sampidevkit/PIC16FDevKit/TUT/B02_Config_GPIO/Cfg_GPIO_XC8.pdf

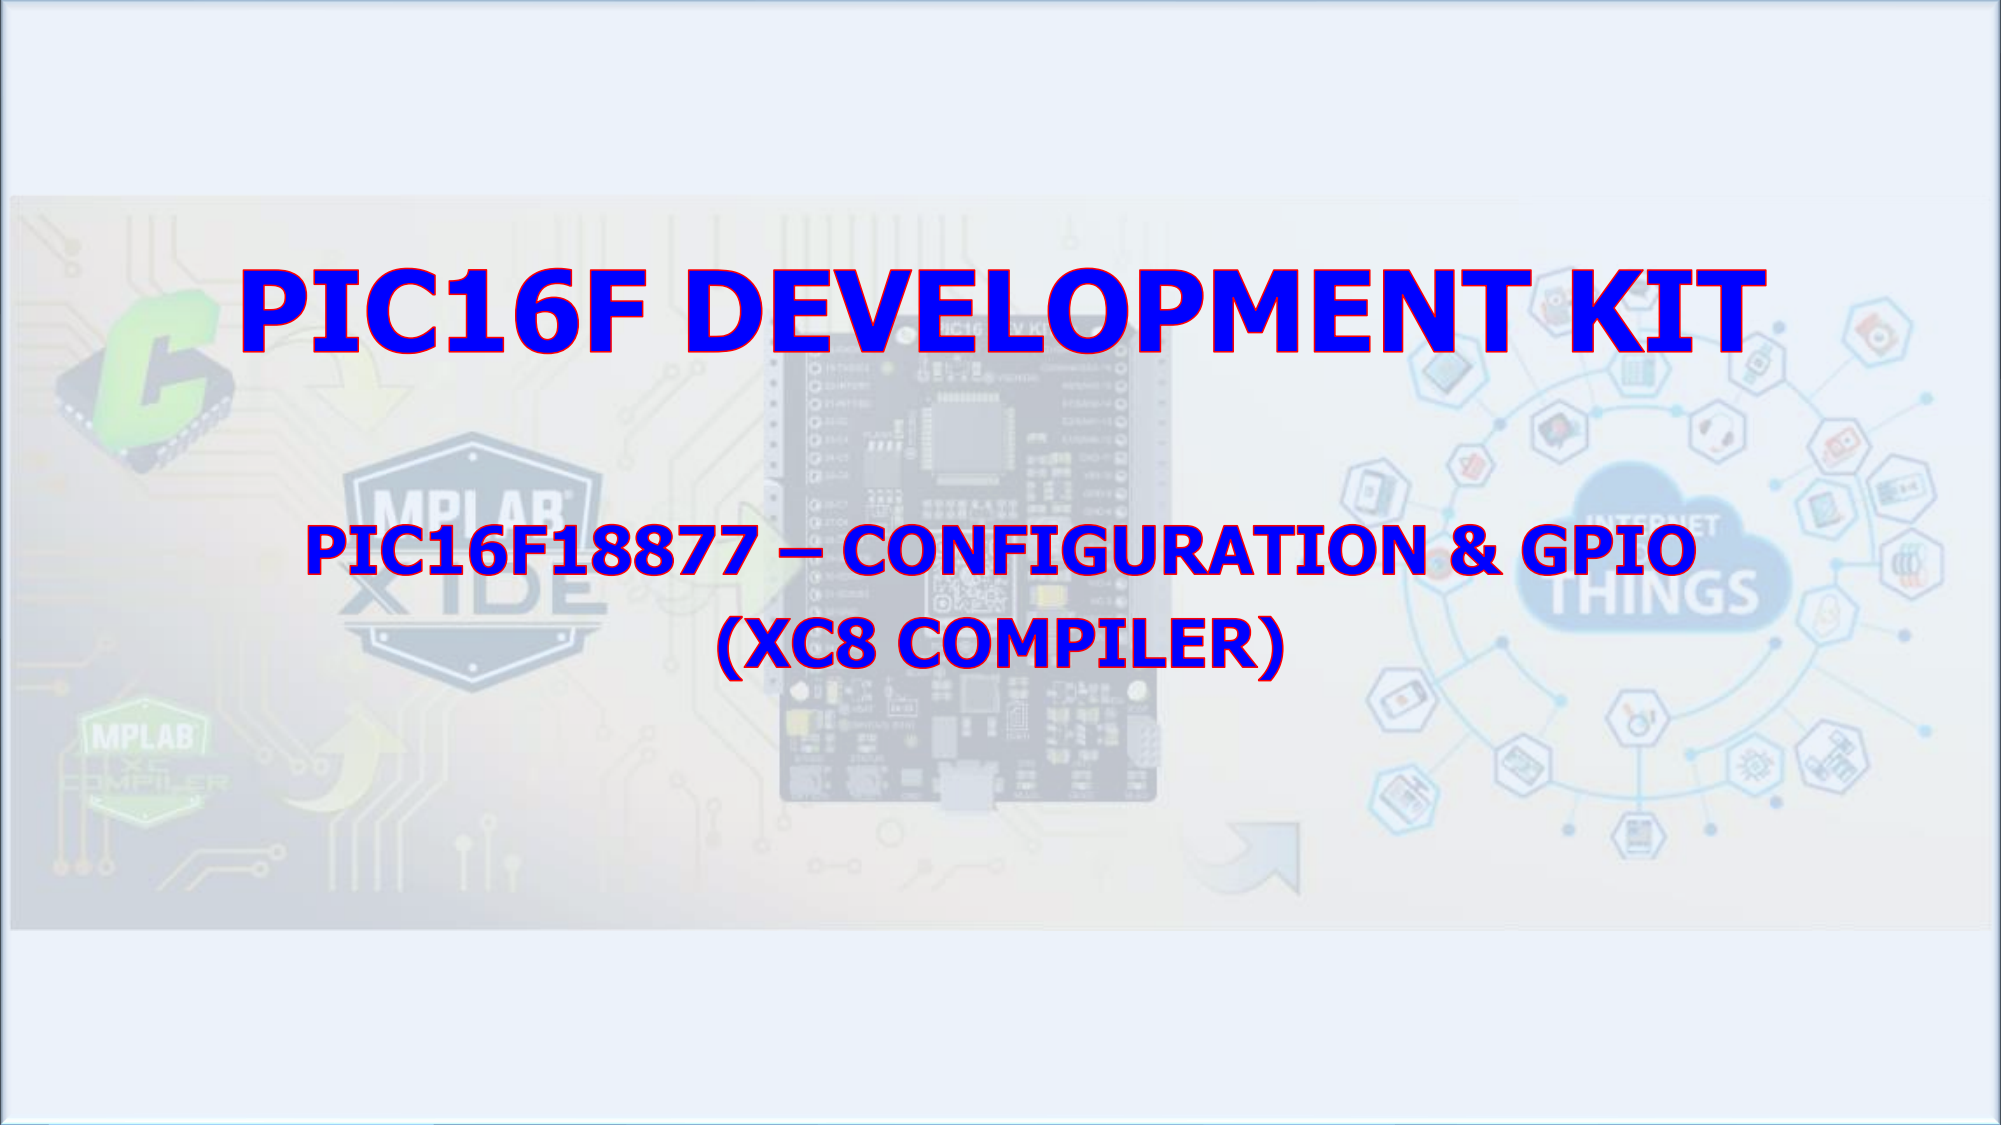
[picture p91: page 1]

# NỘI DUNG

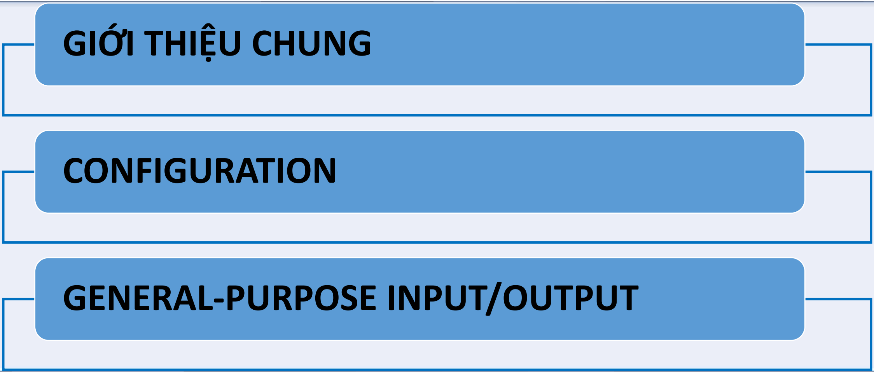
[picture p92: figure]
GIỚI THIỆU CHUNG; CONFIGURATION; GENERAL-PURPOSE INPUT/OUTPUT

# GIỚI THIỆU CHUNG

# 1. HỆ THỐNG VI ĐIỀU KHIỂN

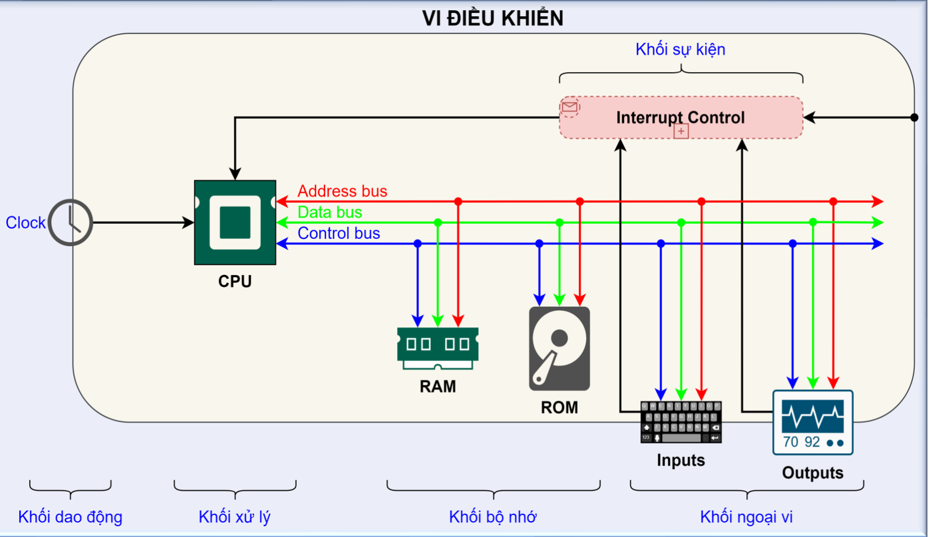
[picture p93: figure]

# 1. Khối dao động 2. Khối xử lý 3. Khối bộ nhớ 4. Khối ngoại vi 5. Khối sự kiện 6. Các khối khác:

Quản lý nguồn,

# Gỡ lỗi, …

GIỚI THIỆU CHUNG

CONFIGURATION

GENERAL-PURPOSE INPUT/OUTPUT

# GIỚI THIỆU CHUNG

# 2. CÔNG CỤ PHÁT TRIỂN

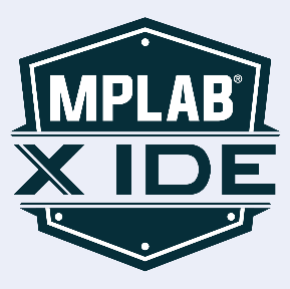
[picture p94: figure]

# 1. MPLAB X IDE/ PIC C IDE Môi trường soạn thảo, định dạng, gỡ lỗi, …

# 2. MPLAB XC8/ CCS C

Chuyển đổi ngôn ngữ C/Asm sang mã thực thi.

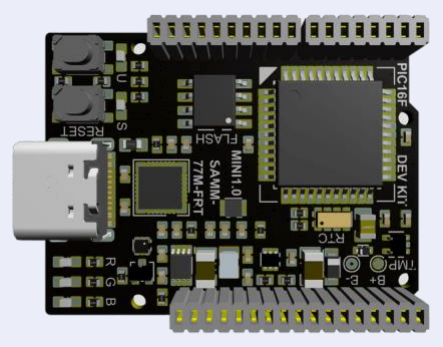
[picture p95: figure]

# 3. Evaluation Kit

GIỚI THIỆU CHUNG

CONFIGURATION

GENERAL-PURPOSE INPUT/OUTPUT

# GIỚI THIỆU CHUNG

# 3. TÀI LIỆU KỸ THUẬT

1. Datasheet: DS40001825F (https://ww1.microchip.com/downloads/en/DeviceDoc/PIC16LF1885777_Data_Sheet_40001825F.pdf)
2. Programming Specifications: DS40001753B (https://ww1.microchip.com/downloads/en/DeviceDoc/40001753B.pdf)

# 3. Application Notes:

# https://www.microchip.com/en-us/application-notes

# 4. Code Examples:

# https://www.microchip.com/doclisting/CodeExamplesByFunc.aspx

GIỚI THIỆU CHUNG

CONFIGURATION

GENERAL-PURPOSE INPUT/OUTPUT

# CONFIGURATION

# 1. CẤU TRÚC BỘ NHỚ

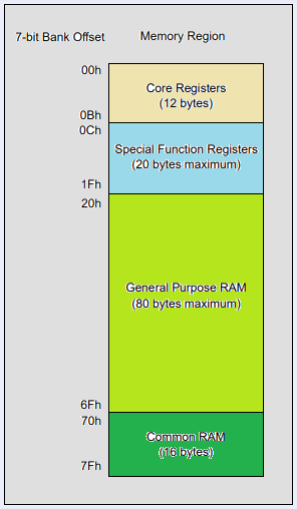
[picture p96: figure]

# Để làm việc với vi điều khiển cần:

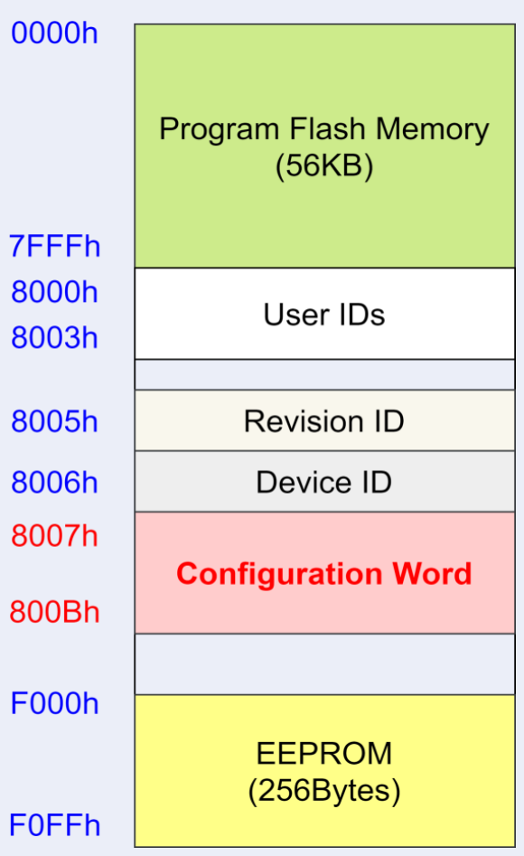
[picture p97: figure]

❑ Cấu hình được chip.
❑ Quản lý được bộ nhớ.
❑ Quản lý được ngoại vi.

# Xem thêm:

→DS40001753B (https://ww1.microchip.com/downloads/en/DeviceDoc/40001753B.pdf) – trang 3.
→DS40001825F (https://ww1.microchip.com/downloads/en/DeviceDoc/PIC16LF1885777_Data_Sheet_40001825F.pdf) – trang 39.

GIỚI THIỆU CHUNG

CONFIGURATION

GENERAL-PURPOSE INPUT/OUTPUT

# CONFIGURATION

# 2. CẤU HÌNH CHIP

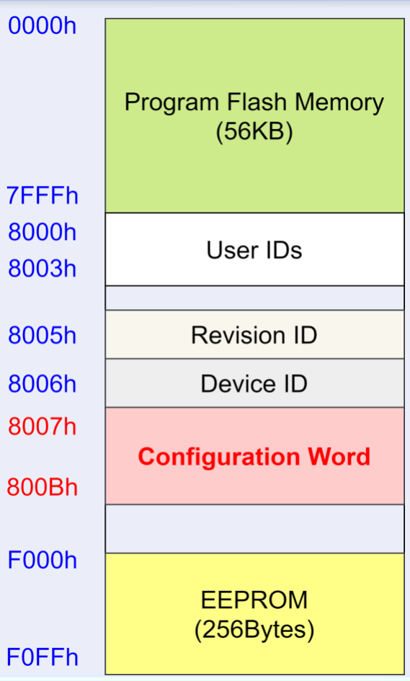
[picture p98: figure]

# ❑ Quy định các tính năng cụ thể của chip, bao gồm: dao động, quản lý lỗi, quản lý nguồn, tính năng bảo mật, …

# ❑ Các bit cấu hình là cố định, không thay đổi trong quá

trình hoạt động.

# ❑ Vùng nhớ cấu hình chip có độ dài 5 word (5x2byte):

## Word 1: Oscillator Word 2: Supervisors Word 3: Watchdog Word 4: Memory Word 5: Code protection

GIỚI THIỆU CHUNG

CONFIGURATION

GENERAL-PURPOSE INPUT/OUTPUT

# CONFIGURATION

# 2. CẤU HÌNH CHIP

GIỚI THIỆU CHUNG

CONFIGURATION

GENERAL-PURPOSE INPUT/OUTPUT

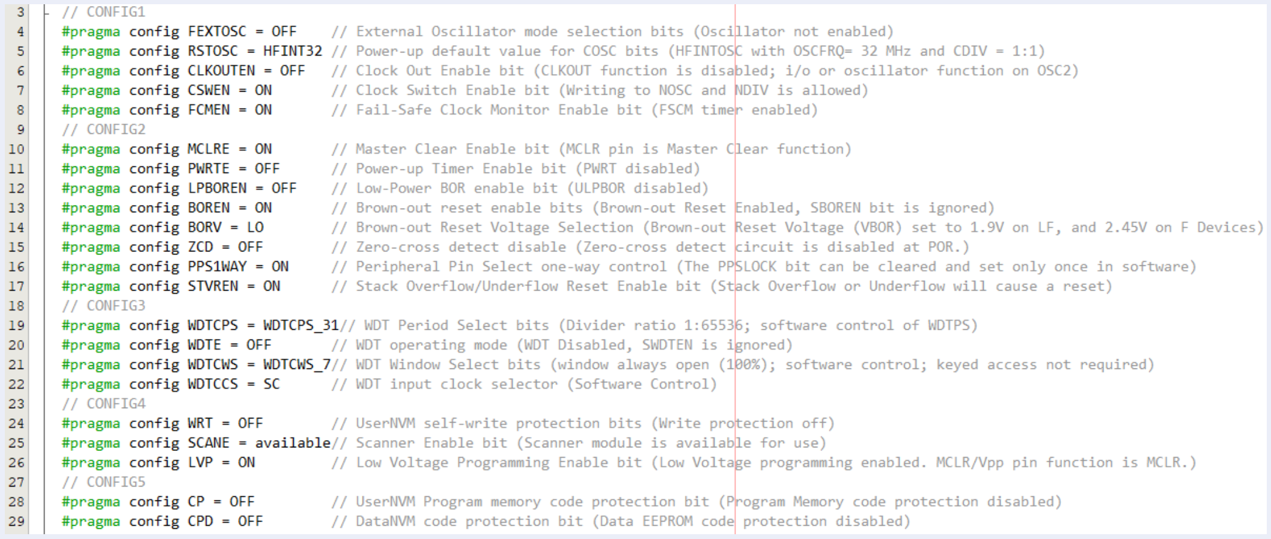
[picture p99: figure]

# CONFIGURATION

# 3. CẤU DAO ĐỘNG

# ❑ PIC16F18877 có 2 nhóm dao động:

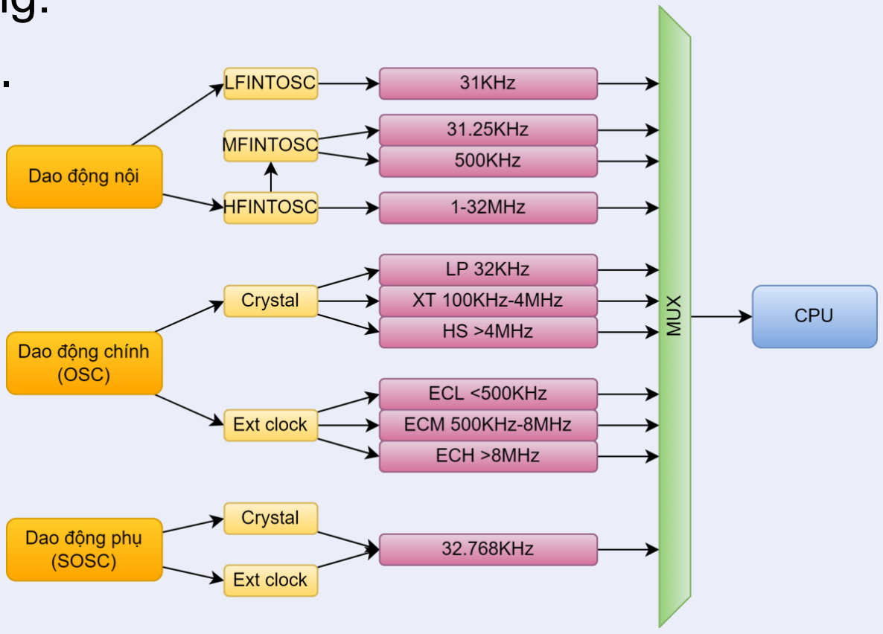
[picture p100: figure]

- Dao động nội: 31KHz đến 32MHz.

# - Dao động ngoài:

- Clock chính OSC: lên đến 32MHz.
- Clock phụ SOSC: 32768Hz.
❑ Tốc độ xử lý: FCPU=FOSC/4.

GIỚI THIỆU CHUNG

CONFIGURATION

GENERAL-PURPOSE INPUT/OUTPUT

# CONFIGURATION

# 3. CẤU DAO ĐỘNG

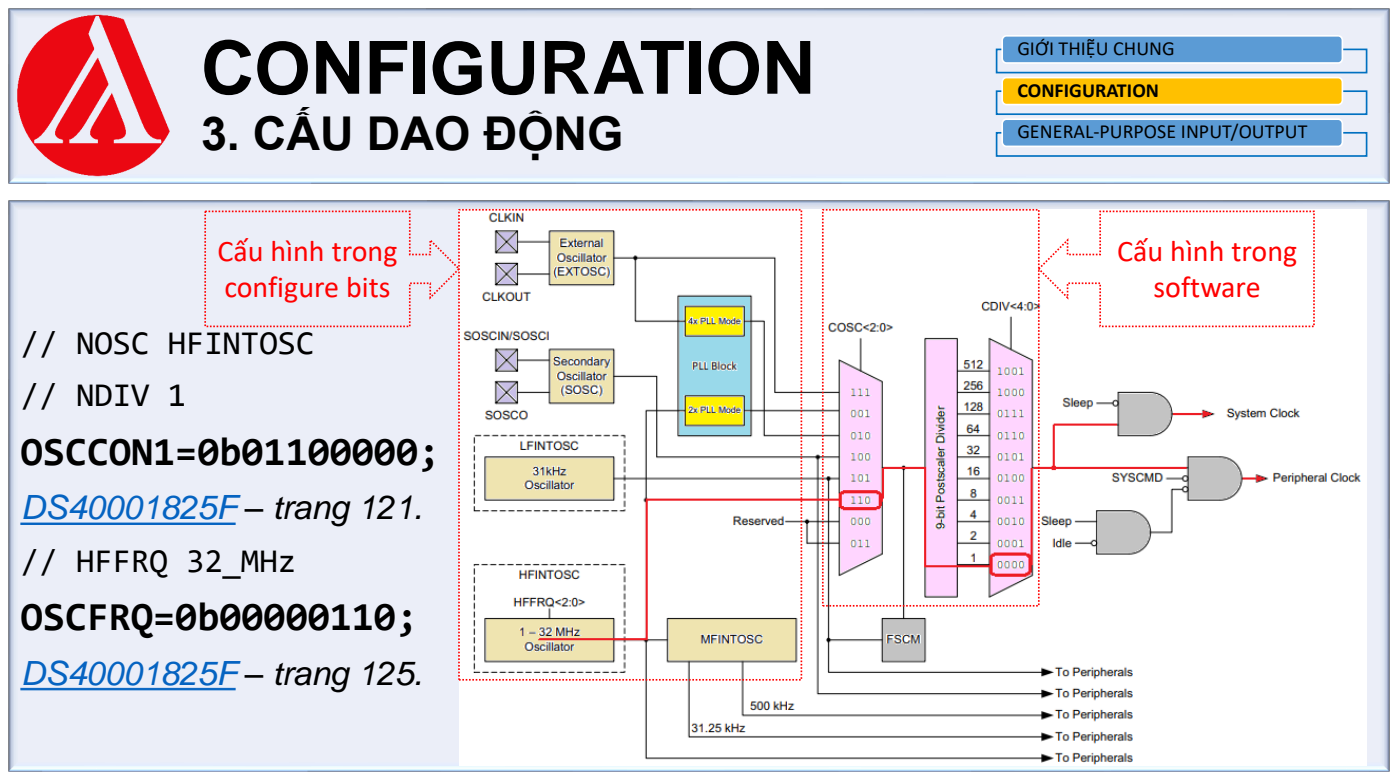
[picture p101: page 10]

## // NOSC HFINTOSC // NDIV 1

OSCCON1=0b01100000;

DS40001825F (https://ww1.microchip.com/downloads/en/DeviceDoc/PIC16LF1885777_Data_Sheet_40001825F.pdf) – trang 121.

## // HFFRQ 32_MHz

OSCFRQ=0b00000110;

DS40001825F (https://ww1.microchip.com/downloads/en/DeviceDoc/PIC16LF1885777_Data_Sheet_40001825F.pdf) – trang 125.

GIỚI THIỆU CHUNG

CONFIGURATION

GENERAL-PURPOSE INPUT/OUTPUT

## Cấu hình trong software

## Cấu hình trong configure bits

# GPIO

# 1. I/O PORTS

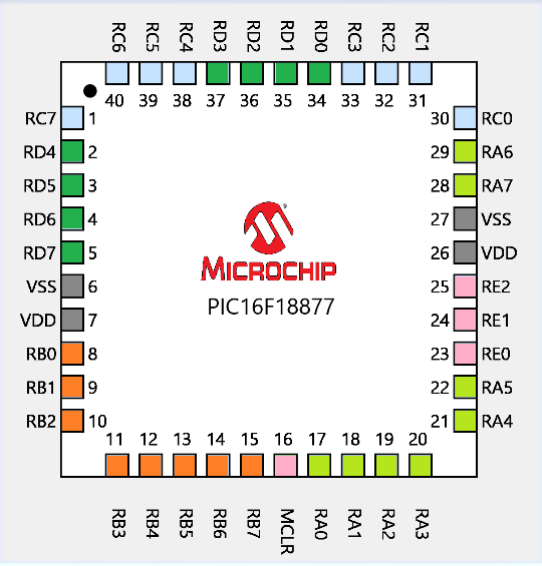
[picture p102: figure]

# ❑ PIC16F18877 có 5 port:

Port A, B, C, D: 8 I/O.

# Port E: 4 I/O. Có 1 I/O được mặc định

chức năng MCLR.

GIỚI THIỆU CHUNG

CONFIGURATION

GENERAL-PURPOSE INPUT/OUTPUT

# GPIO

# 1. I/O PORTS

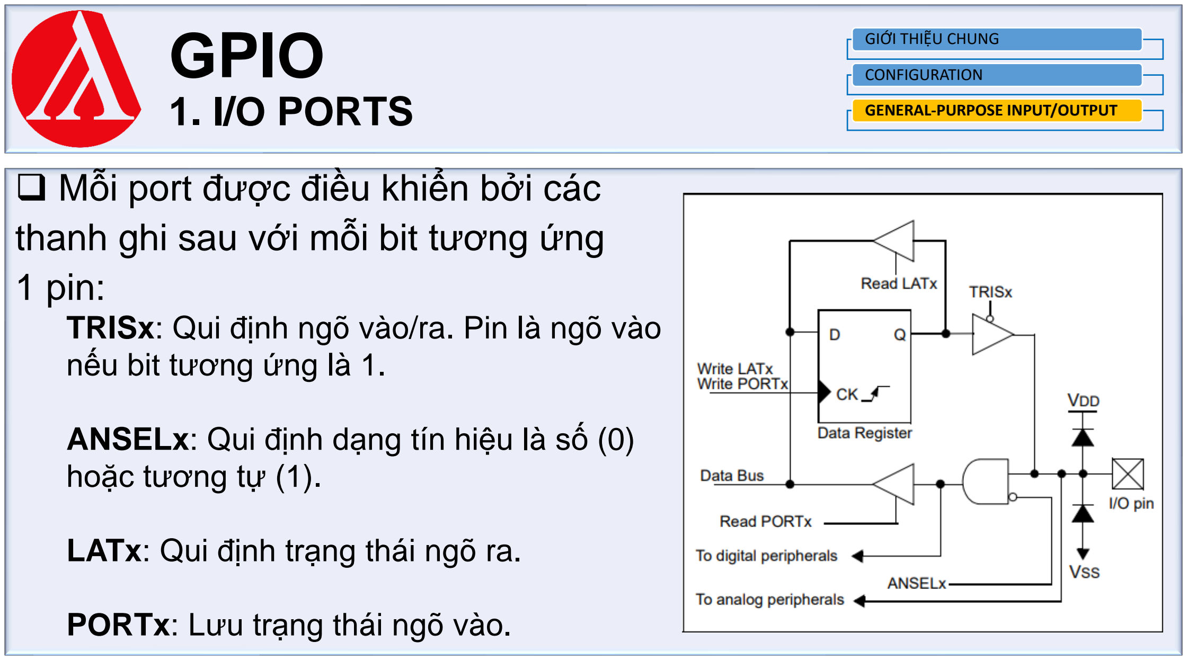
[picture p103: page 12]

# ❑ Mỗi port được điều khiển bởi các thanh ghi sau với mỗi bit tương ứng 1 pin:

# TRISx: Qui định ngõ vào/ra. Pin là ngõ vào

nếu bit tương ứng là 1.

# ANSELx: Qui định dạng tín hiệu là số (0)

hoặc tương tự (1).

LATx: Qui định trạng thái ngõ ra.

PORTx: Lưu trạng thái ngõ vào.

GIỚI THIỆU CHUNG

CONFIGURATION

GENERAL-PURPOSE INPUT/OUTPUT

# GPIO

# 1. I/O PORTS

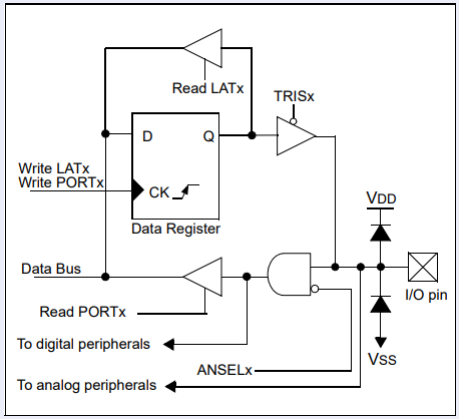
[picture p104: figure]

WPUx: Cấu hình điện trở kéo lên.

# INLVLx: Qui định chuẩn logic TTL hoặc CMOS. (Mặc định)

# SLRCONx: Qui định tốc độ thay đổi trạng thái. (Mặc định)

# ODCONx: Cấu hình ngõ ra cực

nguồn hở.

GIỚI THIỆU CHUNG

CONFIGURATION

GENERAL-PURPOSE INPUT/OUTPUT

# GPIO

# 2. DIGITAL OUTPUTS

# Qui trình cấu hình:

✓ Cấu hình tín hiệu số: ANSELxbits.ANSxy=0;
✓ Cấu hình ngõ ra: TRISxbits.TRISxy=0;

# ✓ Cấu hình cực nguồn: ODCONxbits.ODCxy=0; // Push-Pull

| ODCONxbits.ODCxy=1; // Open-drain
✓ Đặt trạng thái: | LATxbits.LATxy=0; // Set low
| LATxbits.LATxy=1; // Set high

GIỚI THIỆU CHUNG

CONFIGURATION

GENERAL-PURPOSE INPUT/OUTPUT

# GPIO

# 2. DIGITAL OUTPUTS

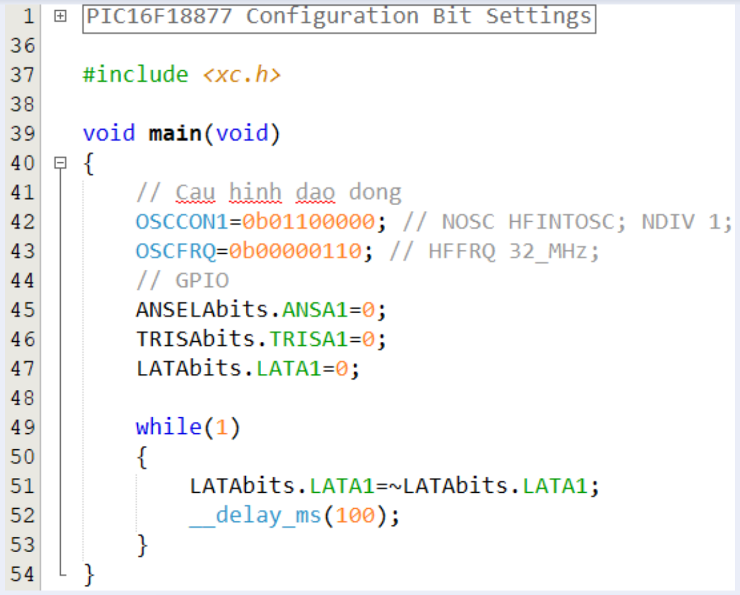
[picture p105: figure]

# Ví dụ:

GIỚI THIỆU CHUNG

CONFIGURATION

GENERAL-PURPOSE INPUT/OUTPUT

# GPIO

# 3. DIGITAL INPUTS

# Qui trình cấu hình:

✓ Cấu hình tín hiệu số: ANSELxbits.ANSxy=0;
✓ Cấu hình ngõ vào: TRISxbits.TRISxy=1;

# ✓ Cấu hình điện trở kéo: WPUAbits.WPUxy=0; // No pull-up

| WPUAbits.WPUxy=1; // Pull-up
✓ Đọc trạng thái: | bool x=PORTxbits.Rxy;

GIỚI THIỆU CHUNG

CONFIGURATION

GENERAL-PURPOSE INPUT/OUTPUT

# GPIO

# 3. DIGITAL INPUTS

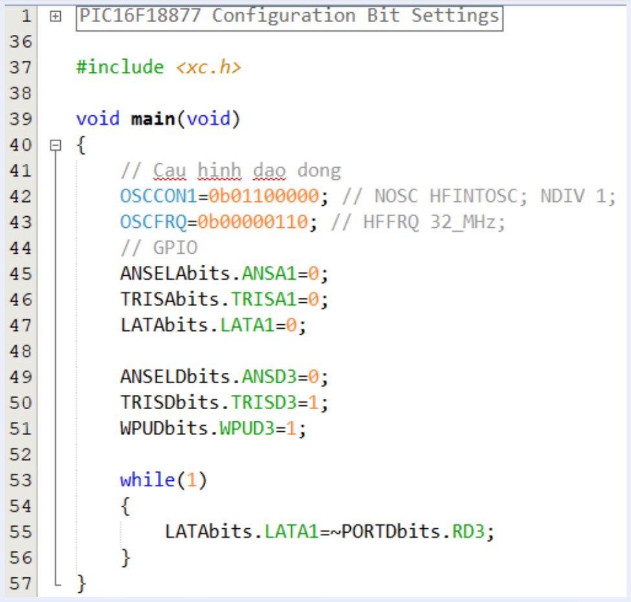
[picture p106: figure]

# Ví dụ

:

GIỚI THIỆU CHUNG

CONFIGURATION

GENERAL

-PURPOSE INPUT/OUTPUT

# GPIO

# 3. DIGITAL INPUTS

# Simple button:

GIỚI THIỆU CHUNG

CONFIGURATION

GENERAL-PURPOSE INPUT/OUTPUT

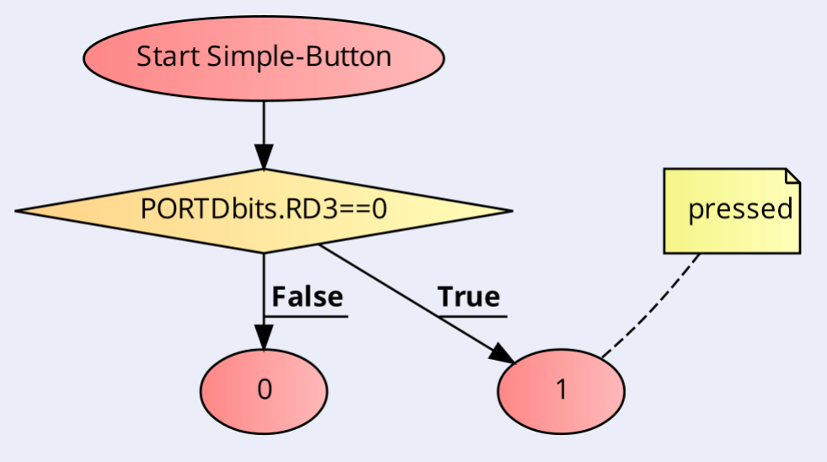
[picture p107: figure]

# GPIO

# 3. DIGITAL INPUTS

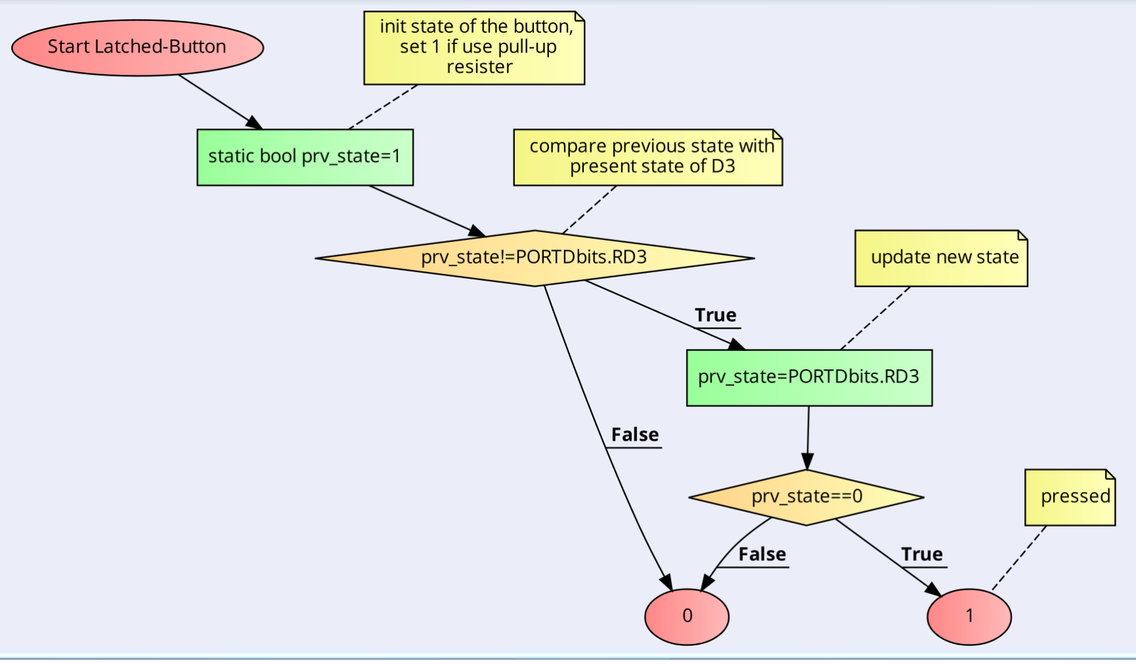
[picture p108: figure]

# Latched button:

GIỚI THIỆU CHUNG

CONFIGURATION

GENERAL-PURPOSE INPUT/OUTPUT

# GPIO

# 3. DIGITAL INPUTS

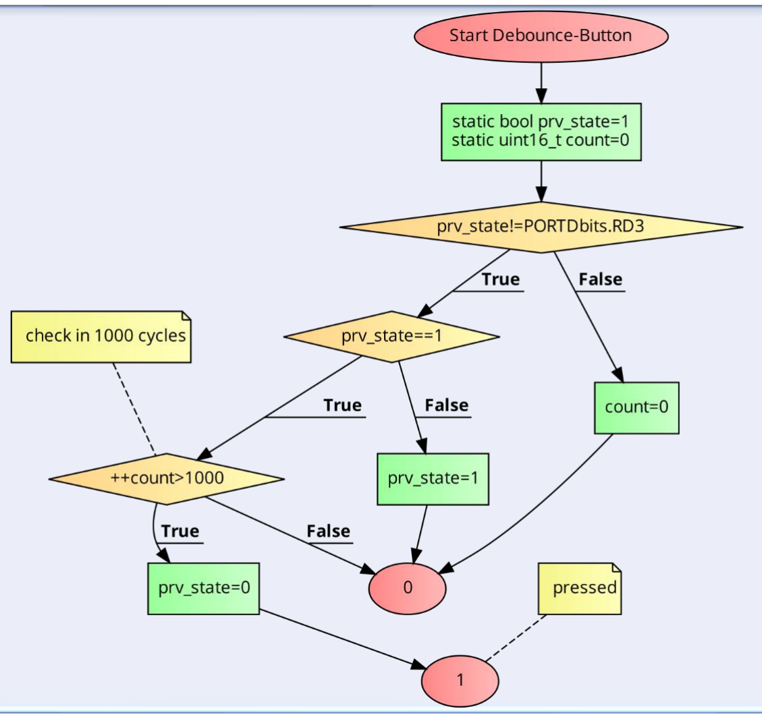
[picture p109: figure]

# Debounce button:

GIỚI THIỆU CHUNG

CONFIGURATION

GENERAL-PURPOSE INPUT/OUTPUT
