sampidevkit/PIC16FDevKit/Docs/Ports.png

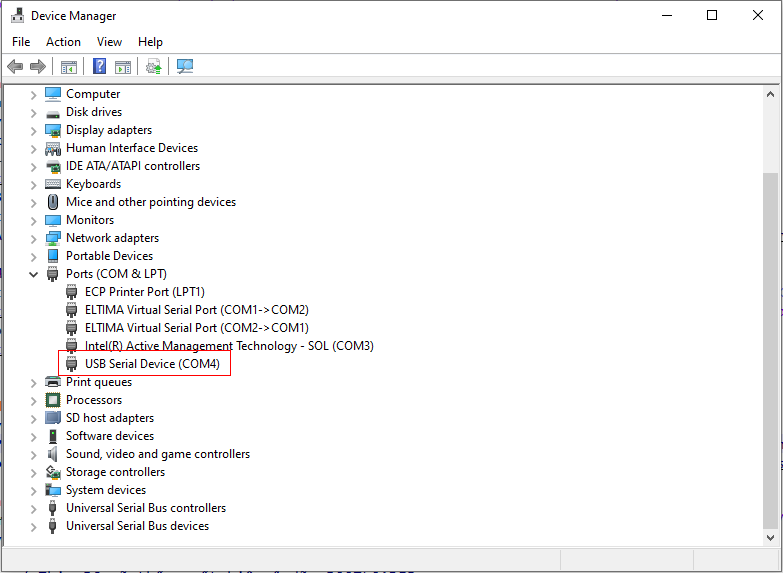
Docs/Ports.png
