sampidevkit/PIC16FDevKit/Docs/Qwiic.bmp

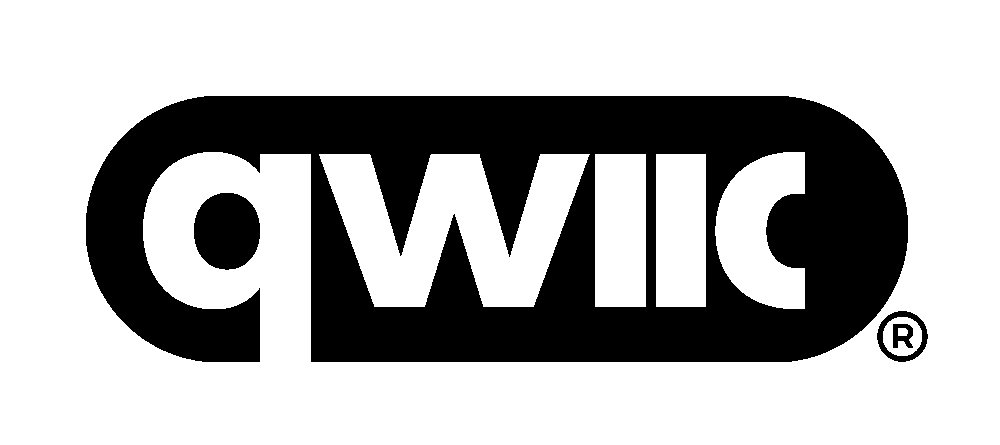
Docs/Qwiic.bmp
