sampidevkit/PIC16FDevKit/Docs/TerminalCfg.png

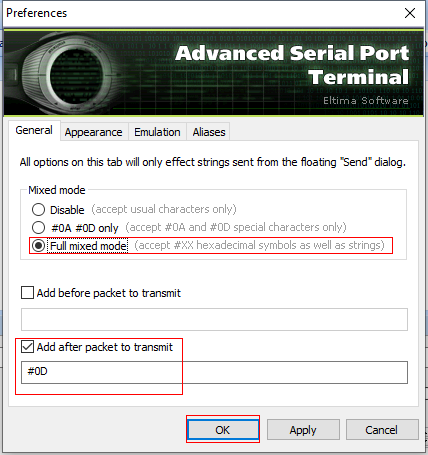
Docs/TerminalCfg.png
