sampidevkit/PIC16FDevKit/Docs/TerminalOpen.png

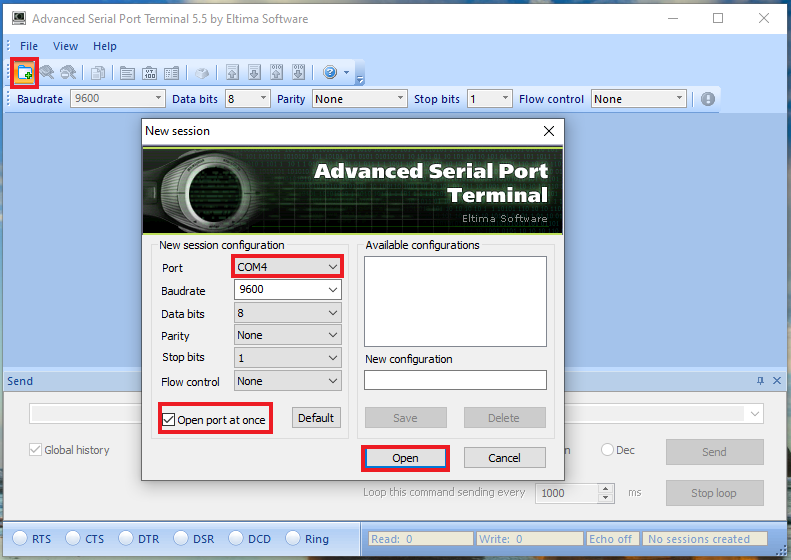
Docs/TerminalOpen.png
