sampidevkit/PIC16FDevKit/Docs/TrainingProgram.drawio.png

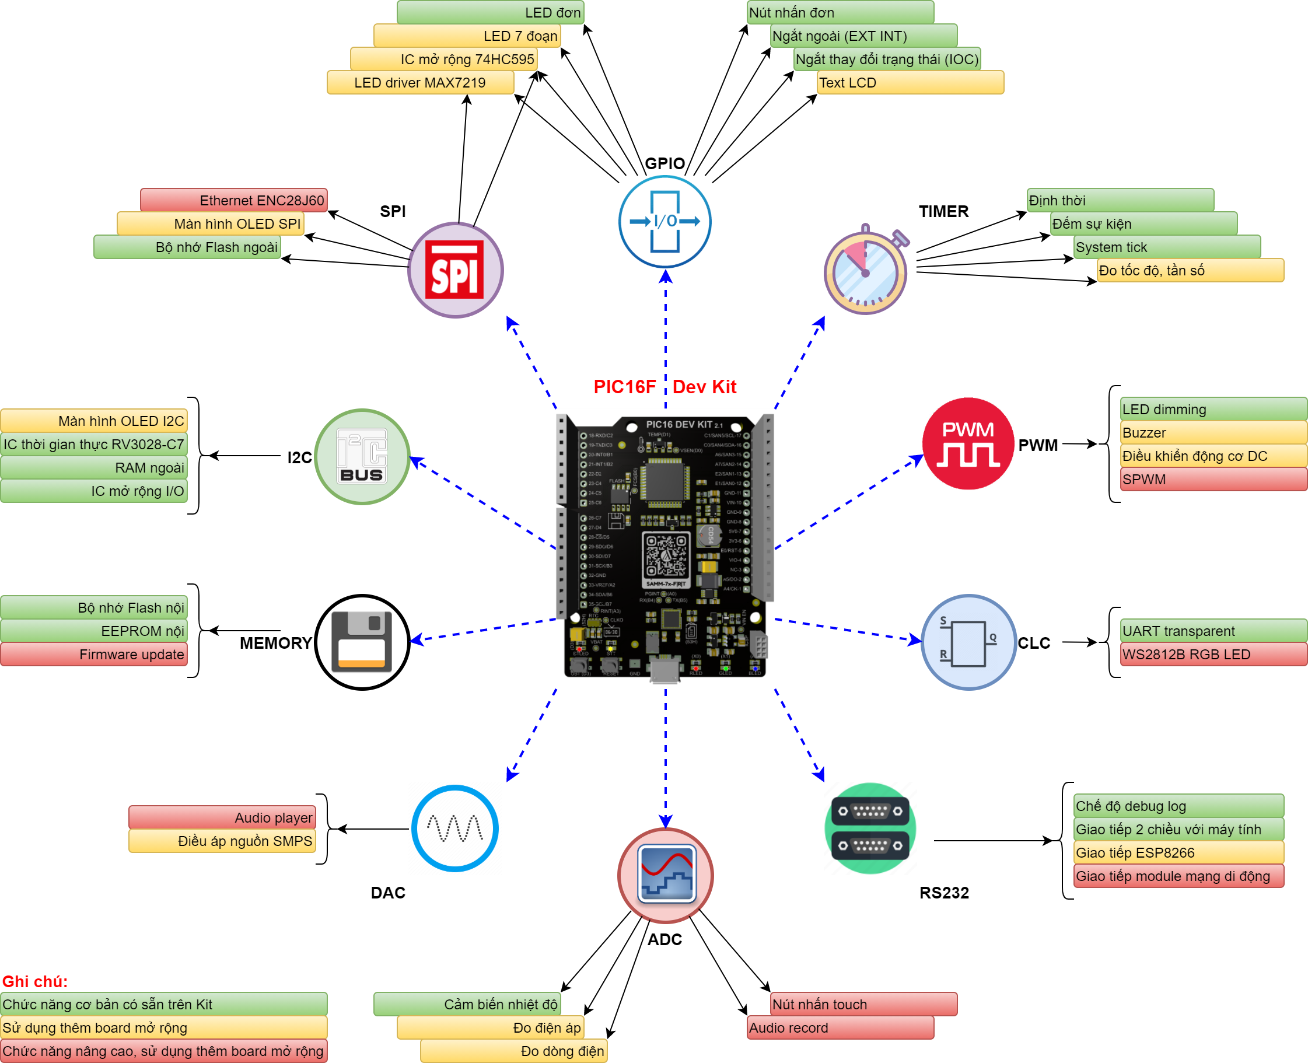
Docs/TrainingProgram.drawio.png
