sampidevkit/PIC16FDevKit/FW/PG_v2.X/App Project Tree.png

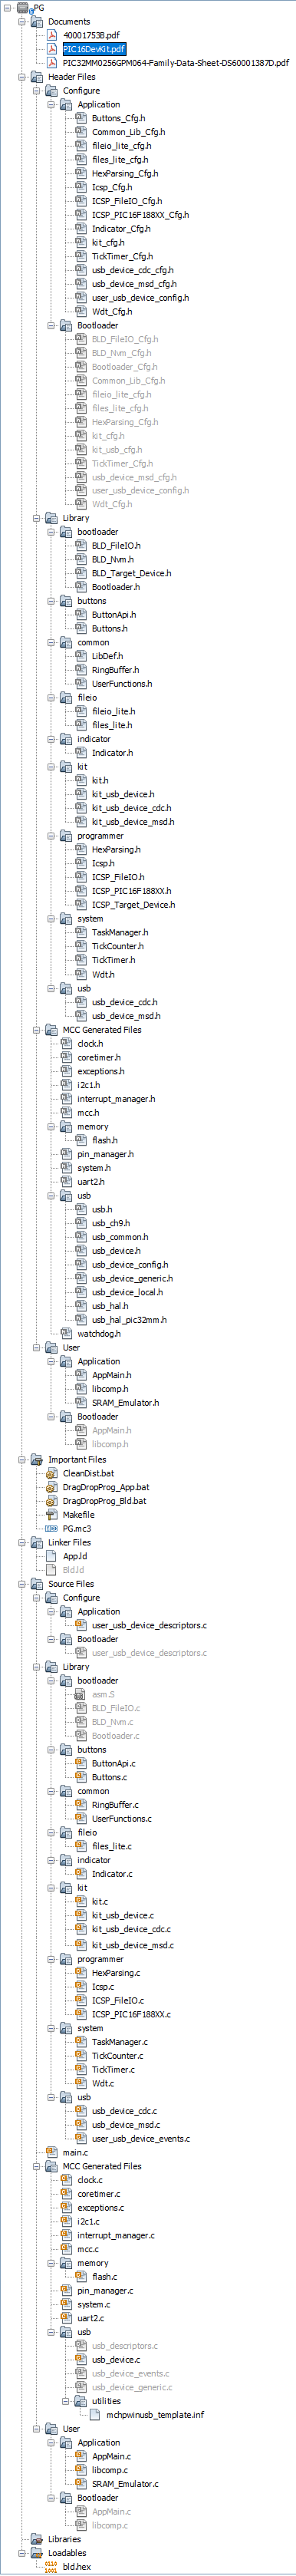
FW/PG_v2.X/App Project Tree.png
