sampidevkit/PIC16FDevKit/FW/PG_v2.X/BLD Project Tree.png

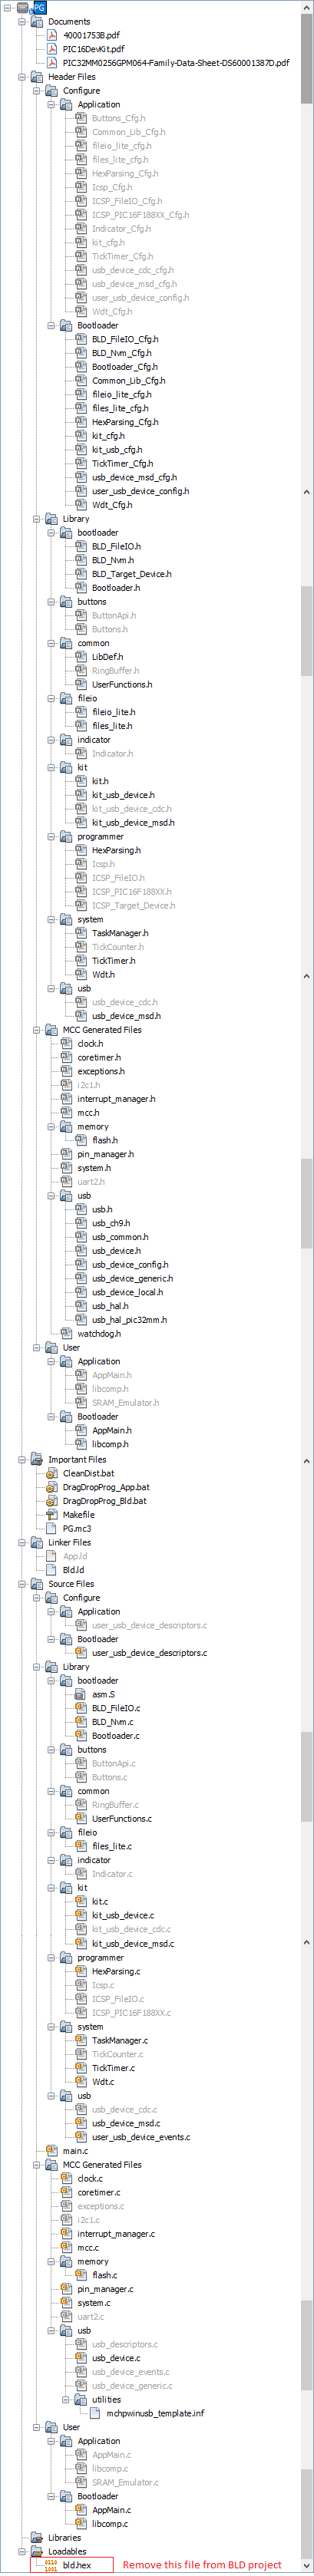
FW/PG_v2.X/BLD Project Tree.png
