sampidevkit/PIC16FDevKit/FW/TG_v2.X/ScreenShot_20220130204213.png

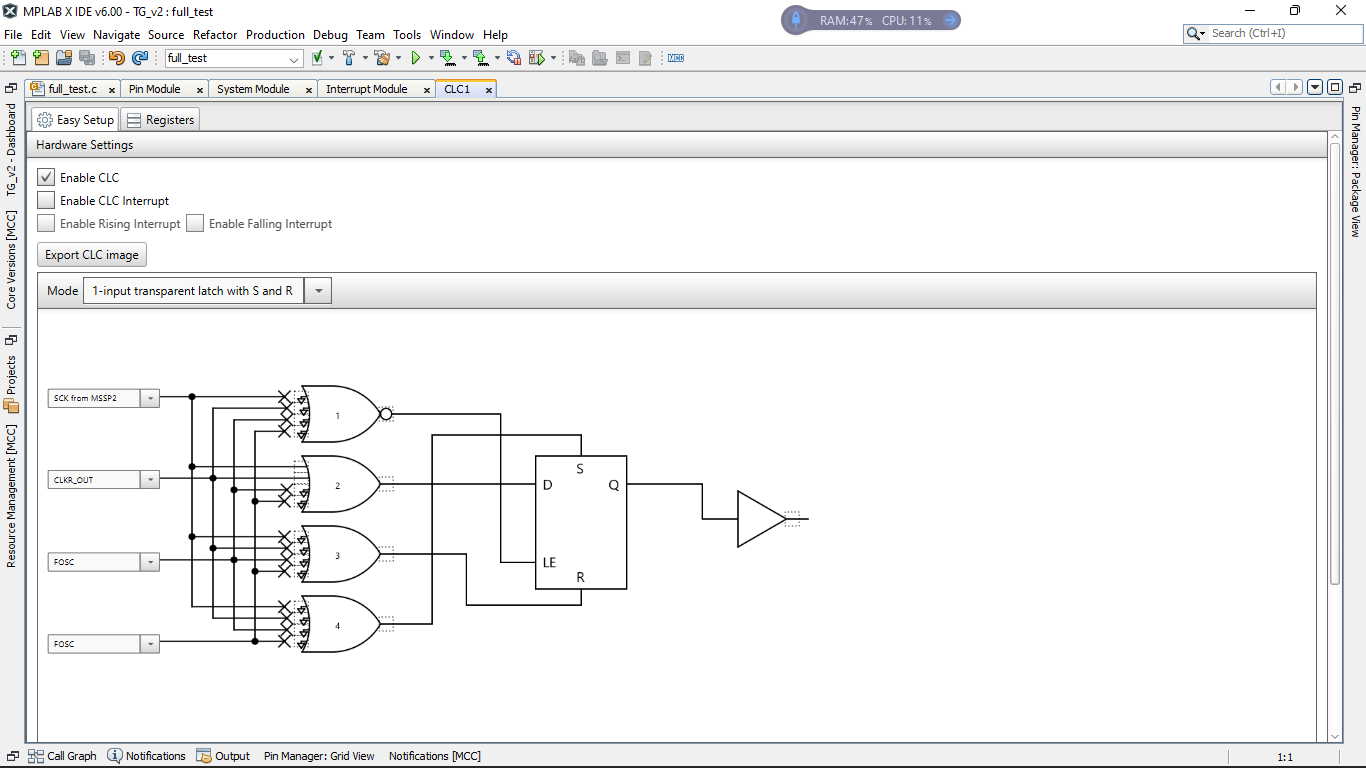
FW/TG_v2.X/ScreenShot_20220130204213.png
