sampidevkit/PIC16FDevKit/HW/Product/Mini/Picture/ScreenShot_20220119223752.png

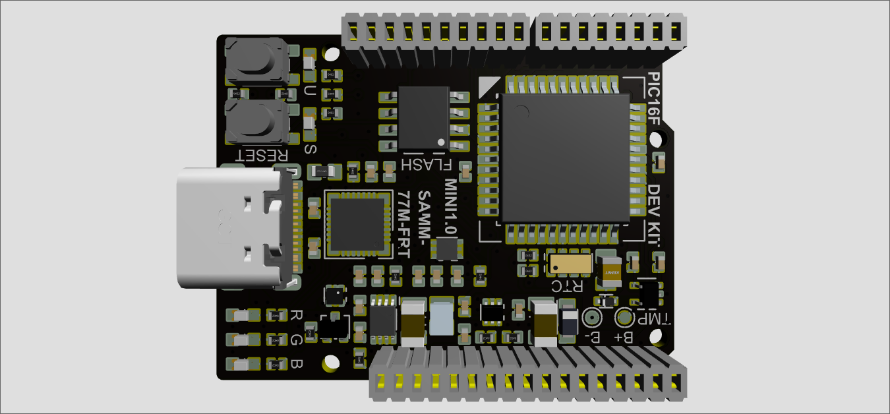
HW/Product/Mini/Picture/ScreenShot_20220119223752.png
