sampidevkit/PIC16FDevKit/HW/Product/Mini/Picture/ScreenShot_20220119223829.png

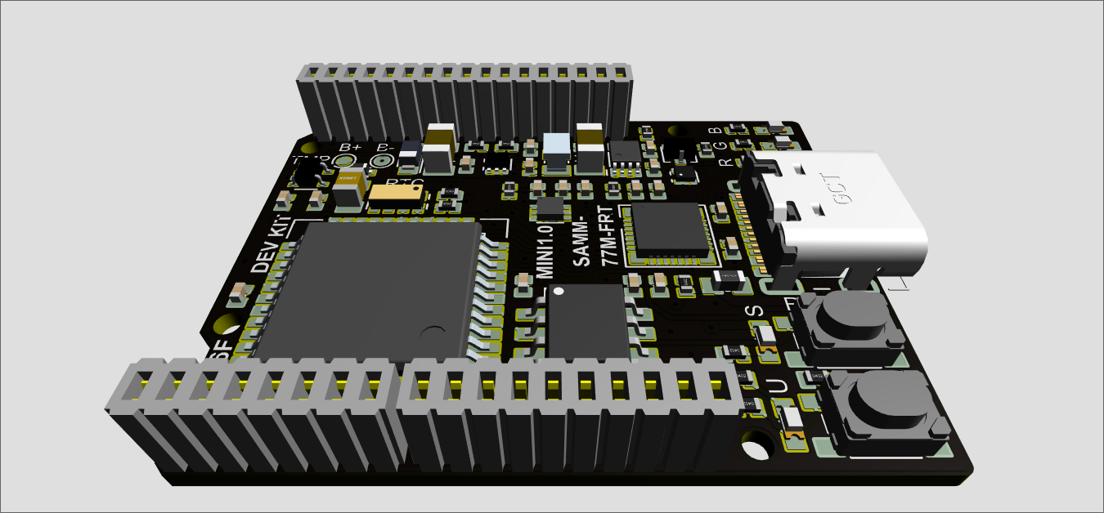
HW/Product/Mini/Picture/ScreenShot_20220119223829.png
