sampidevkit/PIC16FDevKit/HW/Product/Standard/Picture/PIC16DevKit Asm.png

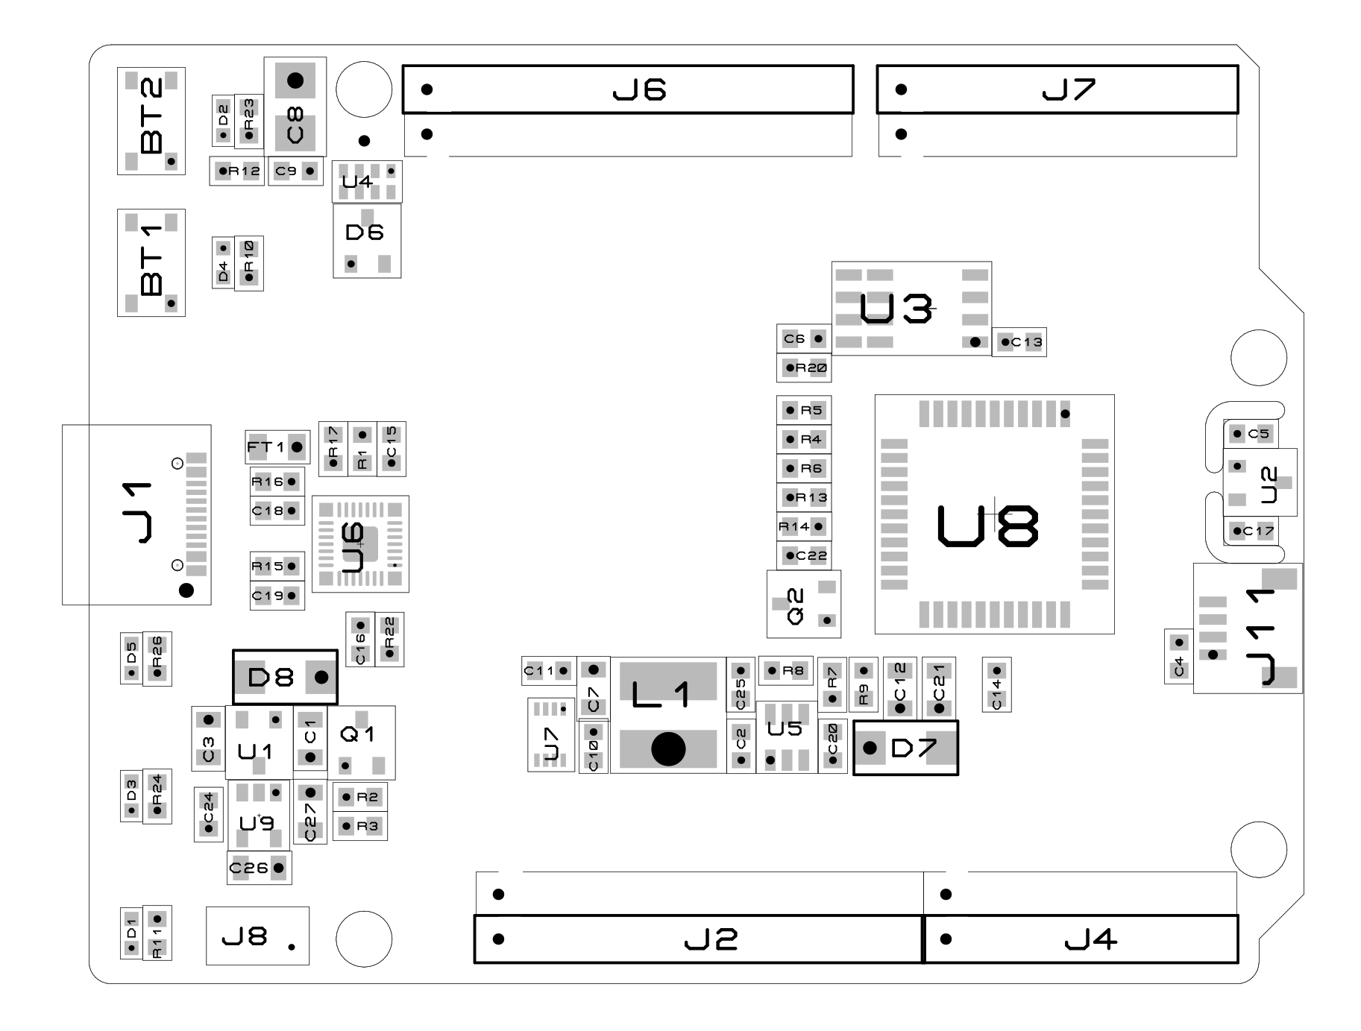
HW/Product/Standard/Picture/PIC16DevKit Asm.png
