sampidevkit/PIC16FDevKit/HW/Product/Standard/Picture/PIC16DevKit Top.png

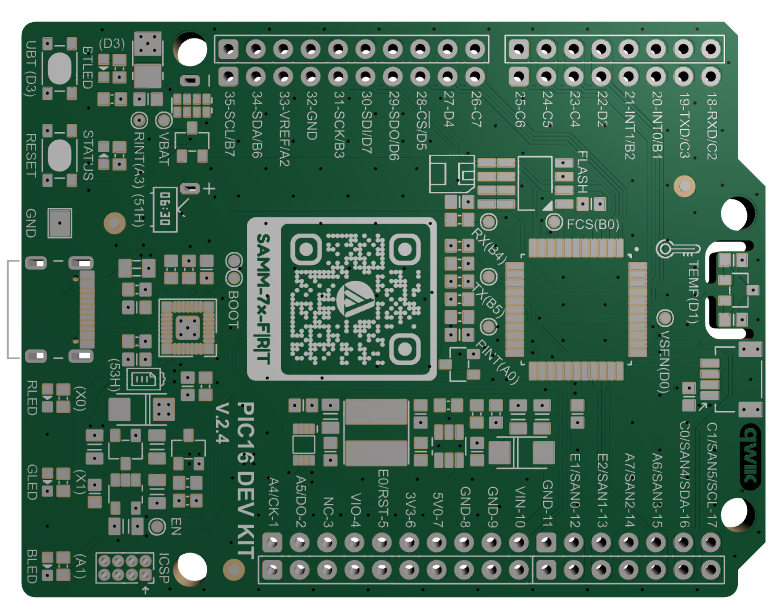
HW/Product/Standard/Picture/PIC16DevKit Top.png
