sampidevkit/PIC16FDevKit/HW/Product/Standard/Picture/PIC16DevKit.png

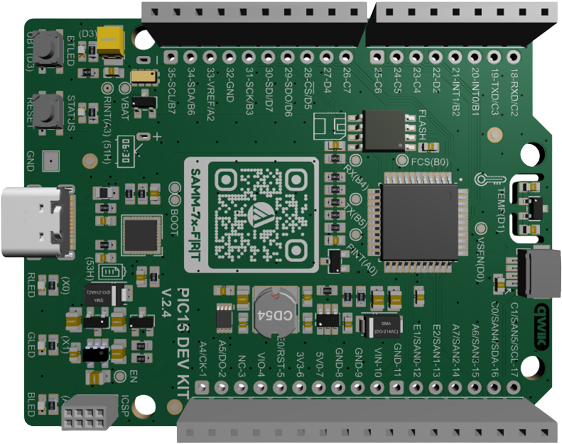
HW/Product/Standard/Picture/PIC16DevKit.png
