sampidevkit/PIC16FDevKit/TUT/B02_Config_GPIO/B02_1_XC8.X/B02_1 (10).png

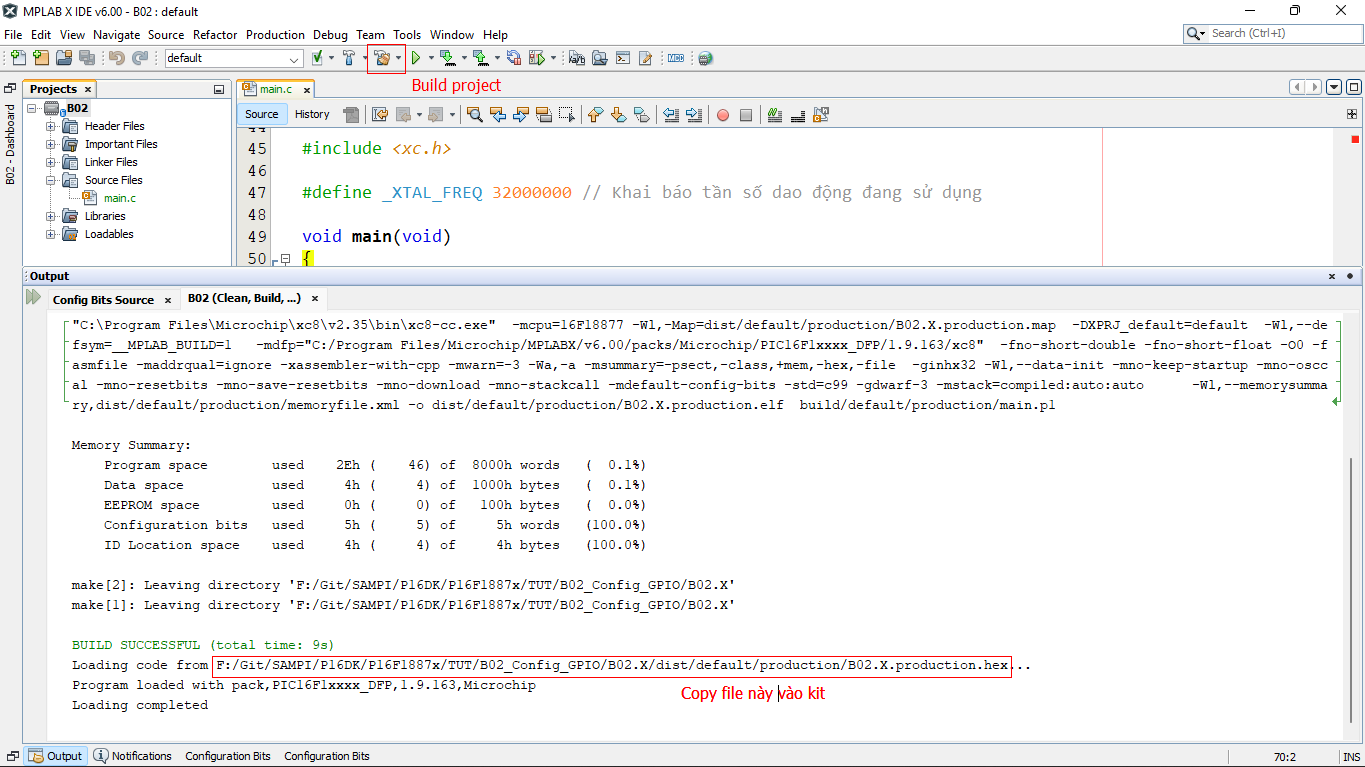
TUT/B02_Config_GPIO/B02_1_XC8.X/B02_1 (10).png
