sampidevkit/PIC16FDevKit/Docs/PIC16DevKit v1.1 Sch.pdf

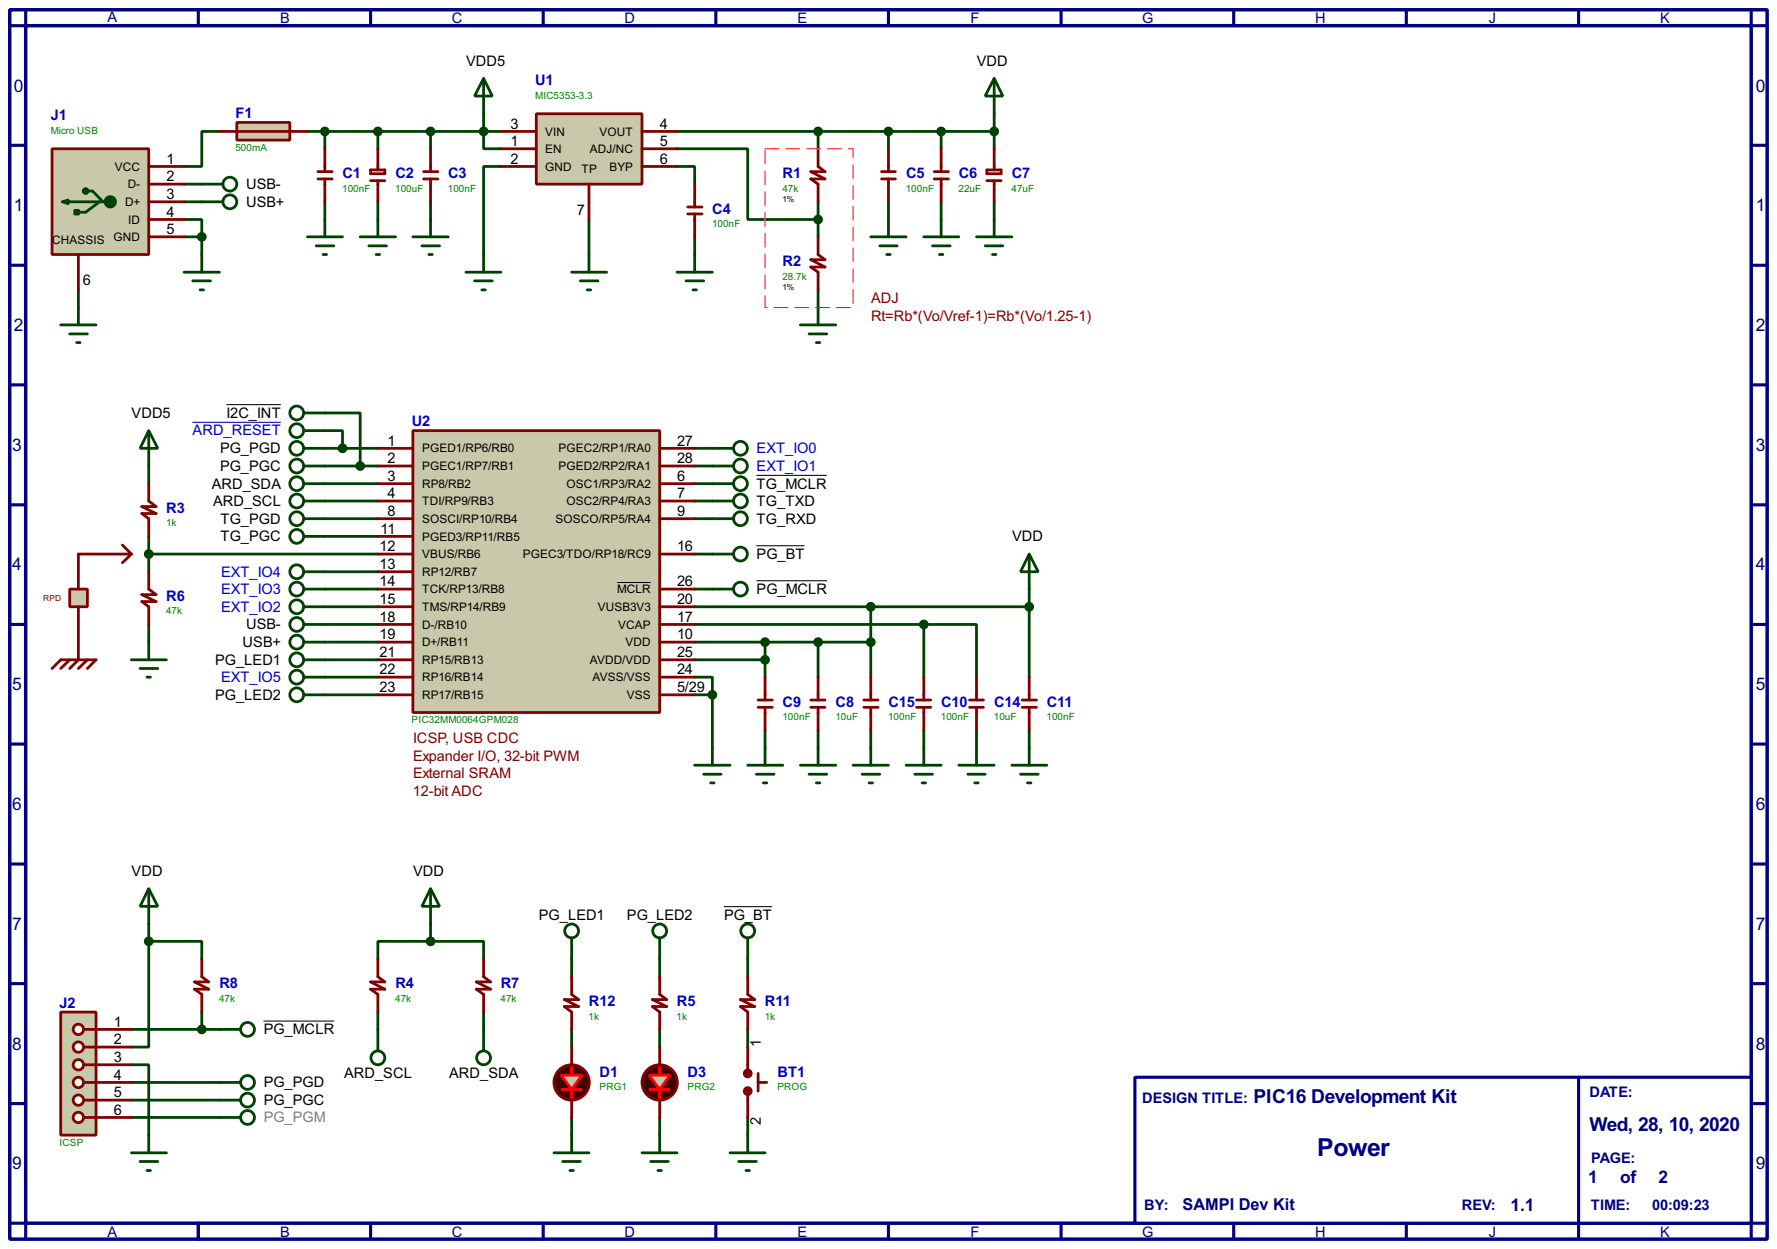
[picture p146: page 1]

ADJ
Rt=Rb*(Vo/Vref-1)=Rb*(Vo/1.25-1)

DESIGN TITLE: PIC16 Development Kit

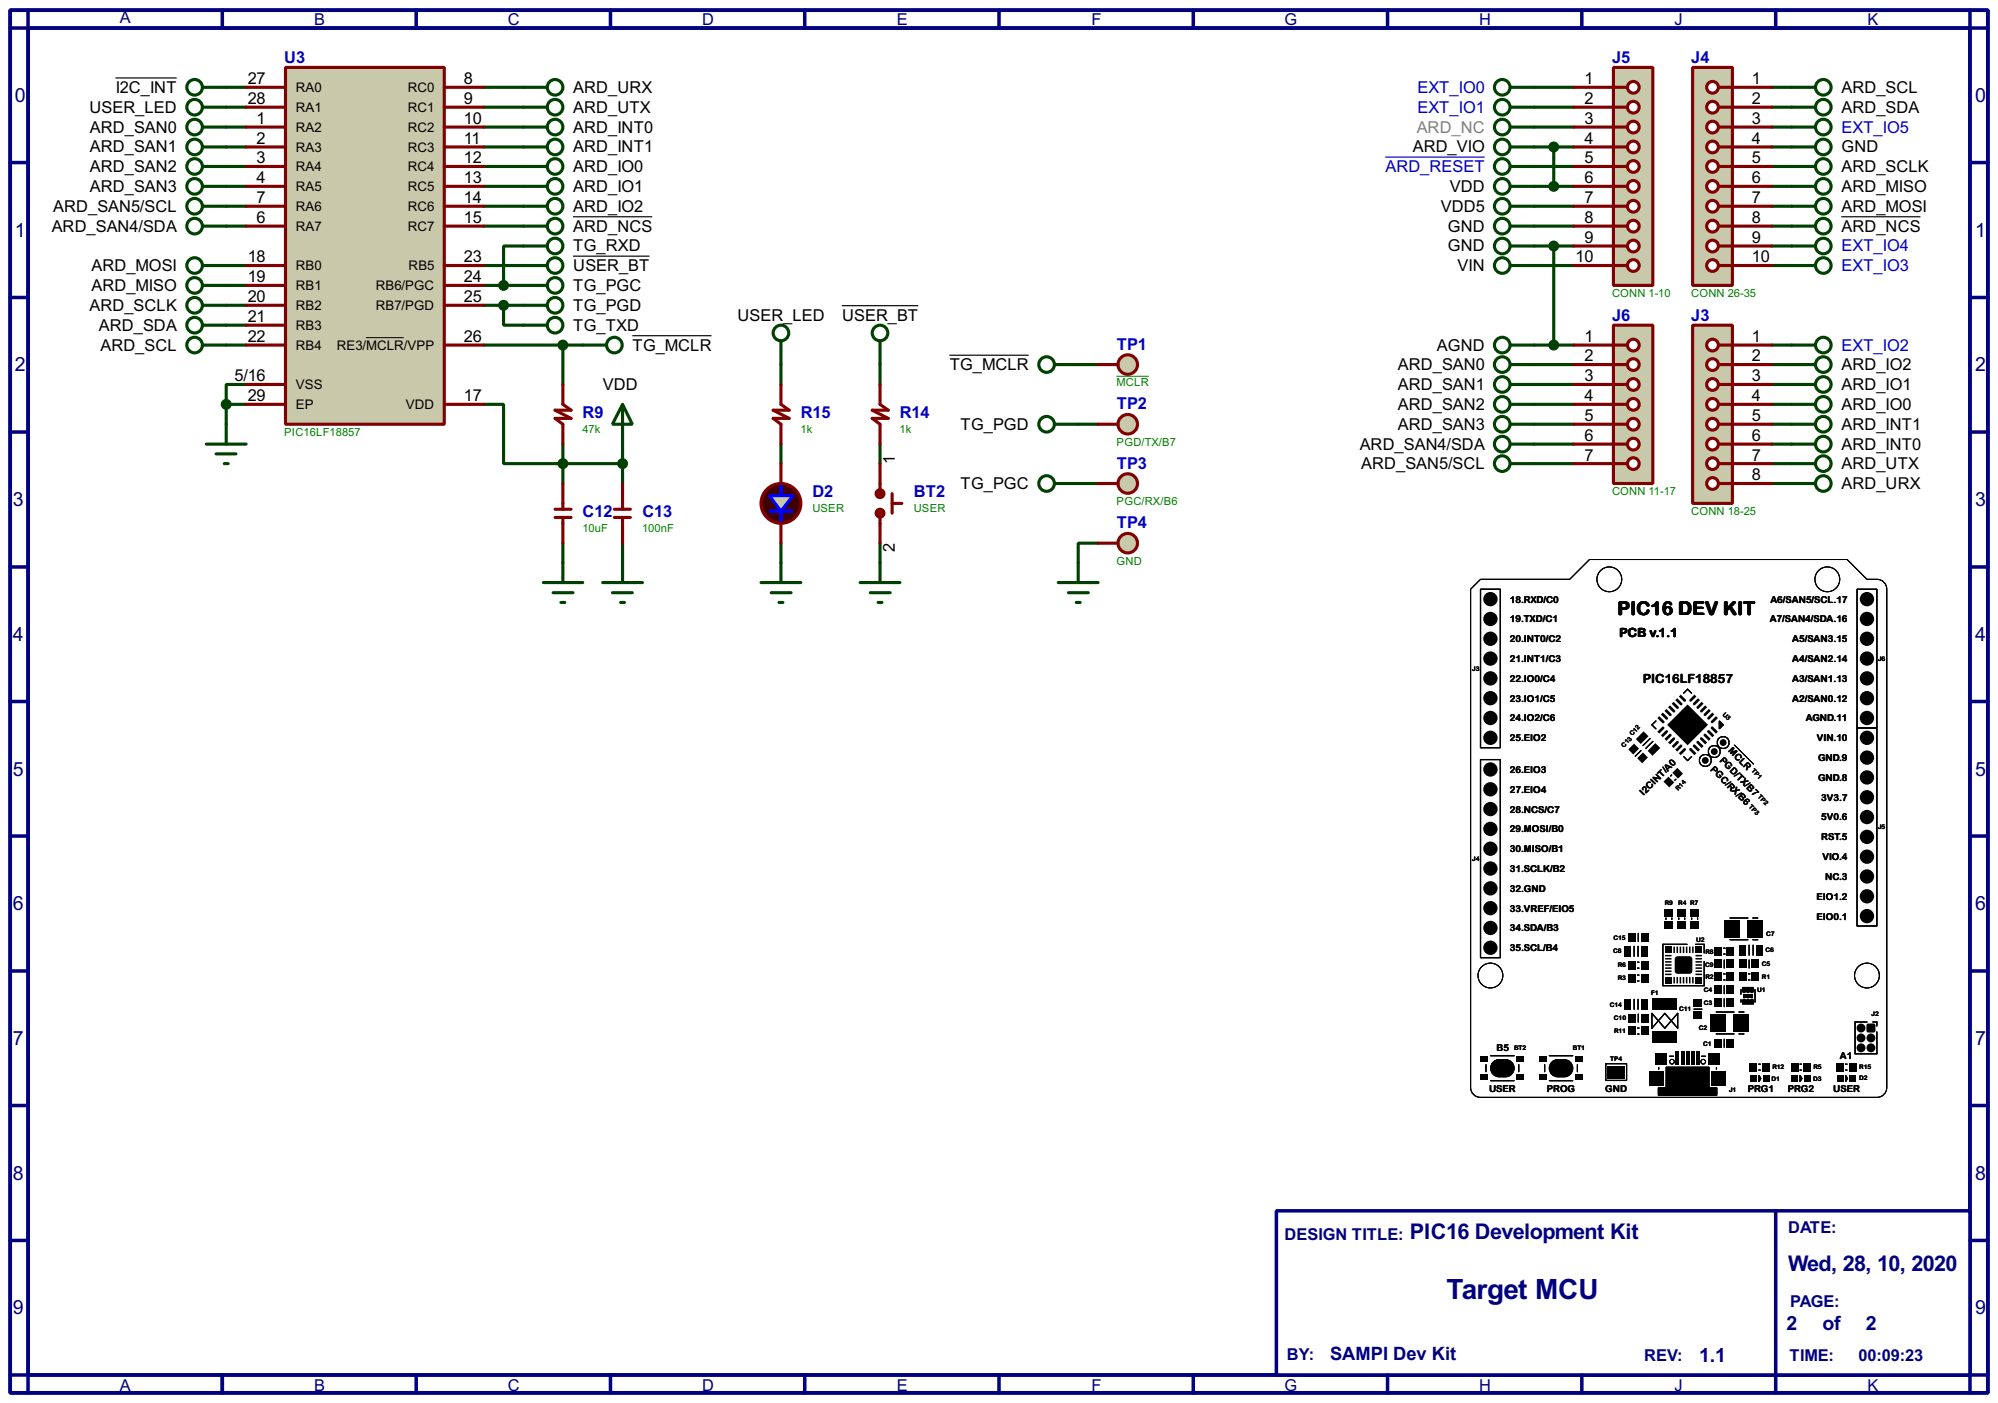
[picture p147: page 2]

CONN 11-17
3V3.7 GND.8 GND.9 VIN.10 A2/SAN0.12 A3/SAN1.13 A4/SAN2.14 A5/SAN3.15 A7/SAN4/SDA.16

3V3.7 GND.8 GND.9 VIN.10 A2/SAN0.12 A3/SAN1.13 A4/SAN2.14 A5/SAN3.15 A7/SAN4/SDA.16 A6/SAN5/SCL.1718.RXD/C0

DESIGN TITLE: PIC16 Development Kit
