sampidevkit/PIC16FDevKit/FW/PG_v2.X/cfg/app/user_usb_device_descriptors.c

#ifndef USER_USB_DESCRIPTORS_C
#define USER_USB_DESCRIPTORS_C

#include "libcomp.h"

/** CONSTANTS ******************************************************/

/* Device Descriptor */
const USB_DEVICE_DESCRIPTOR device_dsc={
    0x12, // Size of this descriptor in bytes
    USB_DESCRIPTOR_DEVICE, // DEVICE descriptor type
    0x0200, // USB Spec Release Number in BCD format
    0xEF, // Class Code "MISC_DEVICE" (ex: uses IAD descriptor)  
    0x02, // Subclass code
    0x01, // Protocol code
    USB_EP0_BUFF_SIZE, // Max packet size for EP0, see usb_config.h
    0x0C00, // Vendor ID  "SAMPI Dev Kit"
    0x0123, // Product ID RS232 Emulation
    0x0001, // Device release number in BCD format
    0x01, // Manufacturer string index
    0x02, // Product string index
    0x03, // Device serial number string index
    0x01 // Number of possible configurations
};

/* Configuration 1 Descriptor */
const uint8_t configDescriptor1[]={
    /* Configuration Descriptor */
    9, // Size of this descriptor in bytes
    USB_DESCRIPTOR_CONFIGURATION, // CONFIGURATION descriptor type
    98, 0, // Total length of data for this cfg
    USB_MAX_EP_NUMBER, // Number of interfaces in this cfg
    1, // Index value of this configuration
    2, // Configuration string index
    _DEFAULT|_SELF, // Attributes, see usb_device.h
    50, // Max power consumption (2X mA)

    //---------------MSD Function 1 Descriptors------------------------
    /* Interface Descriptor */
    9, // Size of this descriptor in bytes
    USB_DESCRIPTOR_INTERFACE, // INTERFACE descriptor type
    MSD_INTF_ID, // Interface Number
    0, // Alternate Setting Number
    2, // Number of endpoints in this intf
    MSD_INTF, // Class code
    MSD_INTF_SUBCLASS, // Subclass code
    MSD_PROTOCOL, // Protocol code
    0, // Interface string index

    /* Endpoint Descriptor */
    7,
    USB_DESCRIPTOR_ENDPOINT,
    MSD_DATA_EP|_EP_IN,
    _BULK,
    MSD_IN_EP_SIZE, 0x00,
    0x01,

    /* Endpoint Descriptor */
    7,
    USB_DESCRIPTOR_ENDPOINT,
    MSD_DATA_EP|_EP_OUT,
    _BULK,
    MSD_OUT_EP_SIZE, 0x00,
    0x01,


    //---------------IAD Descriptor------------------------------------
    /* Interface Association Descriptor: CDC Function 1*/
    0x08, //sizeof(USB_IAD_DSC), // Size of this descriptor in bytes 
    0x0B, // Interface assocication descriptor type 
    CDC_COMM_INTF_ID, // The first associated interface 
    2, // Number of contiguous associated interface 
    COMM_INTF, // bInterfaceClass of the first interface 
    ABSTRACT_CONTROL_MODEL, // bInterfaceSubclass of the first interface 
    V25TER, // bInterfaceProtocol of the first interface 
    0, // Interface string index 						

    //---------------CDC Function 1 Descriptors------------------------

    /* Interface Descriptor: CDC Function 1, Status (communication) Interface */
    0x09, //sizeof(USB_INTF_DSC),   // Size of this descriptor in bytes
    USB_DESCRIPTOR_INTERFACE, // INTERFACE descriptor type
    CDC_COMM_INTF_ID, // Interface Number
    0, // Alternate Setting Number
    1, // Number of endpoints in this intf
    COMM_INTF, // Class code
    ABSTRACT_CONTROL_MODEL, // Subclass code
    V25TER, // Protocol code
    0, // Interface string index

    /* CDC Class-Specific Descriptors */
    //5 bytes: Header Functional Descriptor
    sizeof (USB_CDC_HEADER_FN_DSC), //Size of this descriptor in bytes (5)
    CS_INTERFACE, //bDescriptorType (class specific)
    DSC_FN_HEADER, //bDescriptorSubtype (header functional descriptor)
    0x20, 0x01, //bcdCDC (CDC spec version this fw complies with: v1.20 [stored in little endian])

    //4 bytes: Abstract Control Management Functional Descriptor
    sizeof (USB_CDC_ACM_FN_DSC), //Size of this descriptor in bytes (4)
    CS_INTERFACE, //bDescriptorType (class specific)
    DSC_FN_ACM, //bDescriptorSubtype (abstract control management)
    USB_CDC_ACM_FN_DSC_VAL, //bmCapabilities: (see PSTN120.pdf Table 4)

    //5 bytes: Union Functional Descriptor
    sizeof (USB_CDC_UNION_FN_DSC), //Size of this descriptor in bytes (5)
    CS_INTERFACE, //bDescriptorType (class specific)
    DSC_FN_UNION, //bDescriptorSubtype (union functional)
    CDC_COMM_INTF_ID, //bControlInterface: Interface number of the communication class interface (1)
    CDC_DATA_INTF_ID, //bSubordinateInterface0: Data class interface #2 is subordinate to this interface

    //5 bytes: Call Management Functional Descriptor
    sizeof (USB_CDC_CALL_MGT_FN_DSC), //Size of this descriptor in bytes (5)
    CS_INTERFACE, //bDescriptorType (class specific)
    DSC_FN_CALL_MGT, //bDescriptorSubtype (call management functional)
    0x00, //bmCapabilities: device doesn't handle call management
    CDC_DATA_INTF_ID, //bDataInterface: Data class interface ID used for the optional call management

    /* Endpoint Descriptor */
    0x07, /*sizeof(USB_EP_DSC)*/
    USB_DESCRIPTOR_ENDPOINT, //Endpoint Descriptor
    CDC_COMM_EP|_EP_IN, //EndpointAddress
    _BULK, //Attributes
    CDC_COMM_IN_EP_SIZE, 0x00, //size
    0x02, //Interval

    /* Interface Descriptor: CDC Function 1, Data Interface*/
    0x09, //sizeof(USB_INTF_DSC),   // Size of this descriptor in bytes
    USB_DESCRIPTOR_INTERFACE, // INTERFACE descriptor type
    CDC_DATA_INTF_ID, // Interface Number
    0, // Alternate Setting Number
    2, // Number of endpoints in this intf
    DATA_INTF, // Class code
    0, // Subclass code
    NO_PROTOCOL, // Protocol code
    0, // Interface string index

    /* Endpoint Descriptor */
    //sizeof(USB_EP_DSC),DSC_EP,_EP03_OUT,_BULK,CDC_BULK_OUT_EP_SIZE,0x00,
    0x07, /*sizeof(USB_EP_DSC)*/
    USB_DESCRIPTOR_ENDPOINT, //Endpoint Descriptor
    CDC_DATA_EP|_EP_OUT, //EndpointAddress
    _BULK, //Attributes
    CDC_DATA_OUT_EP_SIZE, 0x00, //size
    0x00, //Interval

    /* Endpoint Descriptor */
    //sizeof(USB_EP_DSC),DSC_EP,_EP03_IN,_BULK,CDC_BULK_IN_EP_SIZE,0x00
    0x07, /*sizeof(USB_EP_DSC)*/
    USB_DESCRIPTOR_ENDPOINT, //Endpoint Descriptor
    CDC_DATA_EP|_EP_IN, //EndpointAddress
    _BULK, //Attributes
    CDC_DATA_IN_EP_SIZE, 0x00, //size
    0x00 //Interval
};

//Language code(s) supported string descriptor

const struct
{
    uint8_t bLength;
    uint8_t bDscType;
    uint16_t string[1];
}

sd000={
    sizeof (sd000),
    USB_DESCRIPTOR_STRING,
    {
        0x0409
    } //0x0409 = Language ID code for US English
};
//Manufacturer string descriptor

const struct
{
    uint8_t bLength;
    uint8_t bDscType;
    uint16_t string[14];
}

sd001={
    sizeof (sd001), USB_DESCRIPTOR_STRING,
    {
        'P', 'L', ' ', 'E', 'l', 'e', 'c', 't', 'r', 'o', 'n', 'i', 'c', 's'
    }
};

//Product string descriptor

const struct
{
    uint8_t bLength;
    uint8_t bDscType;
    uint16_t string[13];
}

sd002={
    sizeof (sd002), USB_DESCRIPTOR_STRING,
    {
        'S', 'A', 'M', 'P', 'I', ' ', 'D', 'e', 'v', ' ', 'K', 'i', 't'
    }
};

//Serial number string descriptor.  Note: This should be unique for each unit 
//built on the assembly line.  Plugging in two units simultaneously with the 
//same serial number into a single machine can cause problems.  Additionally, not 
//all hosts support all character values in the serial number string.  The MSD 
//Bulk Only Transport (BOT) specs v1.0 restrict the serial number to consist only
//of ASCII characters "0" through "9" and capital letters "A" through "F".

struct
{
    uint8_t bLength;
    uint8_t bDscType;
    uint16_t string[12];
}

sd003={
    sizeof (sd003), USB_DESCRIPTOR_STRING,
    {
        '0', '1', '2', '3', '4', '5', '6', '7', '8', '9', 'A', 'B'
    }
};

void USER_USB_Device_LoadUDID(void)
{
    uint32_t udID;
    uint8_t i;

    udID=UDID1;

    for(i=0; i<8; i++)
    {
        sd003.string[i]=Bcd2Hex((uint8_t) (udID&0xF));
        udID>>=4;
    }

    udID=UDID2;

    for(i=0; i<4; i++)
    {
        sd003.string[8+i]=Bcd2Hex((uint8_t) (udID&0xF));
        udID>>=4;
    }
}

//Array of configuration descriptors
const uint8_t*const USB_CD_Ptr[]={
    (const uint8_t*const) &configDescriptor1
};

//Array of string descriptors
const uint8_t*const USB_SD_Ptr[]={
    (const uint8_t*const) &sd000,
    (const uint8_t*const) &sd001,
    (const uint8_t*const) &sd002,
    (const uint8_t*const) &sd003
};

/** EOF usb_descriptors.c ***************************************************/

#endif
