sampidevkit/PIC16FDevKit/FW/PG_v2.X/cfg/app/ICSP_FileIO_Cfg.c

#include "ICSP_FileIO_Cfg.h"
#include "libcomp.h"

bool MediaWriteProtect=0;
uint8_t App_Log_Buffer[APP_BUFFER_LOG_LEN];

int Hardware_Info(uint8_t *pD) // <editor-fold defaultstate="collapsed" desc="Get hardware info">
{

    /* Sample hardware info
            PIC16F Dev Kit SAMM-7x v2.x\n
            Owner: SAMPI\n
            BLD Rel: Dec 11 2021-21:13:4
     -->    APP Rel: mmm dd yyyy-H:m:s
     */
    union
    {
        uint16_t val;

        struct
        {
            unsigned Rfu:8;
            unsigned Thermal:2;
            unsigned Rtcc:2;
            unsigned Flash:4;
        };
    } part_number;

    int i;
    uint8_t flash_name[16];
    uint8_t rtcc_name[16];
    uint8_t thermal_name[24];
    uint8_t *p=(uint8_t*) __INFO_ADDRESS__;

    strcpy(&pD[0], p);
    i=str_1st_index(&pD[0], '\n')+1;
    p=str_first(&pD[i], '\n');
    *p=0x00;
    i=strlen(&pD[0]);
    i+=sprintf(&pD[i], "\nAPP Rel: %s - %s", __DATE__, __TIME__);
    i+=sprintf(&pD[i], "\n%s\n", __WEBSITE__);
    part_number.val=(uint16_t) FDEVOPTbits.USERID;
    i+=sprintf(&pD[i], "\nP/N: SAMM-7x-");

    if(part_number.Flash>0)
        pD[i++]='F';

    if(part_number.Rtcc>0)
        pD[i++]='R';

    if(part_number.Thermal>0)
        pD[i++]='T';

    switch(part_number.Flash)
    {
        case 0b0000:
            strcpy(flash_name, "No flash");
            break;

        case 0b0001:
            strcpy(flash_name, "SST25VF020B");
            break;

        case 0b0010:
            strcpy(flash_name, "SST25VF040B");
            break;

        case 0b0011:
            strcpy(flash_name, "SST25VF080B");
            break;

        case 0b0100:
            strcpy(flash_name, "SST25VF016B");
            break;

        case 0b0101:
            strcpy(flash_name, "SST25VF032B");
            break;

        case 0b0110:
            strcpy(flash_name, "SST25VF064B");
            break;

        case 0b0111:
            strcpy(flash_name, "SST25PF020B");
            break;

        case 0b1000:
            strcpy(flash_name, "SST25PF040C");
            break;

        case 0b1001:
            strcpy(flash_name, "SST25PF080B");
            break;

        case 0b1100:
            strcpy(flash_name, "W25Q32");
            break;

        case 0b1101:
            strcpy(flash_name, "W25Q16");
            break;

        case 0b1110:
            strcpy(flash_name, "GD25Q32");
            break;

        case 0b1111:
            strcpy(flash_name, "GD25Q64");
            break;

        default:
            flash_name[0]=0x00;
            break;
    }

    switch(part_number.Rtcc)
    {
        case 0b00:
            strcpy(rtcc_name, "No RTCC");
            break;

        case 0b01:
            strcpy(rtcc_name, "RV-8263-C7");
            break;

        case 0b10:
            strcpy(rtcc_name, "RV-8803-C7");
            break;

        default:
            rtcc_name[0]=0x00;
            break;
    }

    switch(part_number.Thermal)
    {
        case 0b00:
            strcpy(thermal_name, "No thermal sensor");
            break;

        case 0b01:
            strcpy(thermal_name, "MCP9700");
            break;

        case 0b10:
            strcpy(thermal_name, "MCP9701");
            break;

        default:
            thermal_name[0]=0x00;
            break;
    }

    if(part_number.val==0)
        i+=sprintf(&pD[i], "0000\n");
    else
        i+=sprintf(&pD[i], "-%04X\n", part_number.val);

    i+=sprintf(&pD[i], "%s, %s, %s\n", flash_name, rtcc_name, thermal_name);

    return i;
} // </editor-fold>
