sampidevkit/PIC16FDevKit/FW/PG_v2.X/cfg/app/Buttons_Cfg.h

#ifndef BUTTONS_CFG_H
#define BUTTONS_CFG_H

#include <stdbool.h>

// Reset target MCU
#define SW1_TIMEOUT             200 // ms
#define SW1_TIME_MODE_EDGE_H2L  TIME_MODE_EDGE_H2L
#define SW1_GetValue            ProgButton_GetState
// Enter into bootloader mode
#define SW2_TIMEOUT             3000 // ms
#define SW2_TIME_MODE_EDGE_H2L  TIME_MODE_EDGE_H2L
#define SW2_GetValue            ProgButton_GetState
// Erase target MCU
#define SW3_TIMEOUT             10 // ms
#define SW3_TIME_MODE_EDGE_H2L  TIME_MODE_EDGE_L2H
#define SW3_GetValue            ProgButton_GetState
// ICSP uninitialized check
#define SW4_TIMEOUT             500 // ms
#define SW4_TIME_MODE_EDGE_H2L  TIME_MODE_EDGE_H2L
#define SW4_GetValue            ICSP_Uninitialized_Check

bool ProgButton_GetState(void);
bool ICSP_Uninitialized_Check(void);

#endif
