sampidevkit/PIC16FDevKit/FW/PG_v2.X/cfg/app/ICSP_FileIO_Cfg.h

#ifndef ICSP_FILEIO_CFG_H
#define ICSP_FILEIO_CFG_H

#include <stdbool.h>
#include <stdint.h>

#define USE_BLD_INFO
#define __INFO_ADDRESS__                    0x9D00C000
#define __WEBSITE__                         "https://bit.ly/3rMJ4hs"

#define write_error_log(line)               do{uint32_t err=line; icsp_log(ICSP_LOG_INTERNAL_ERROR, &err, NULL, NULL);}while(0)
#define ICSP_FileIo_WriteProtect_GetState() MediaWriteProtect
#define DRV_CONFIG_DRIVE_CAPACITY           4096 // *512 byte = useable drive volume
#define DRV_SECTORS_PER_CLUSTER             8 // *512 byte = cluster size (4kB)
#define DRV_MAX_NUM_FILES_IN_ROOT           16
#define DRV_NUM_RESERVED_SECTORS            1
#define DRV_NUM_VBR_SECTORS                 1
#define DRV_NUM_FAT_SECTORS                 1

// INFO.txt file
#define APP_BUFFER_LOG_LEN                  128
// ICSP FileIO
extern bool MediaWriteProtect;
extern uint8_t App_Log_Buffer[APP_BUFFER_LOG_LEN];

int Hardware_Info(uint8_t *pD);

#endif
