sampidevkit/PIC16FDevKit/FW/PG_v2.X/cfg/app/Indicator_Cfg.c

#include "Indicator_Cfg.h"
#include "libcomp.h"

void StatusLED_SetState(sled_t Set) // <editor-fold defaultstate="collapsed" desc="Set state of status LED">
{
    static bool locked=0;

LOOP:
    switch(Set)
    {
        case SLED_ACTIVE:
            locked=0;
        case SLED_RESET:
            Indicator_SetHigh(0);
            break;

        case SLED_FAIL:
            locked=1;
            Indicator_SetState(0, 500, 1500, IND_LOOP_FOREVER);
            break;

        case SLED_ONESHOT:
            Indicator_SetState(0, 5, 1, 1);
            break;

        case SLED_IDLE:
        default:
            if(locked==0)
                Indicator_SetState(0, 10, 1990, IND_LOOP_FOREVER);
            else
            {
                Set=SLED_FAIL;
                goto LOOP;
            }
            break;
    }
} // </editor-fold>
