sampidevkit/PIC16FDevKit/FW/PG_v2.X/user/app/libcomp.c

#include "libcomp.h"

public void DummyInterruptHandler(void) // <editor-fold defaultstate="collapsed" desc="Dummy interrupt handler">
{
    // Do nothing
} // </editor-fold>

public void LibComp_Initialize(void) // <editor-fold defaultstate="collapsed" desc="App porting initialize">
{
} // </editor-fold>
