sampidevkit/PIC16FDevKit/FW/PG_v2.X/cfg/app/ICSP_PIC16F188XX_Cfg.h

#ifndef ICSP_PIC16F188XX_CFG_H
#define ICSP_PIC16F188XX_CFG_H

#define TARGET_MCU_PIC16F188XX // All MCUs
//#define TARGET_MCU_PIC16LF18854
//#define TARGET_MCU_PIC16F18854
//#define TARGET_MCU_PIC16LF18855
//#define TARGET_MCU_PIC16F18855
//#define TARGET_MCU_PIC16LF18856
//#define TARGET_MCU_PIC16F18856
//#define TARGET_MCU_PIC16LF18857
//#define TARGET_MCU_PIC16F18857
//#define TARGET_MCU_PIC16LF18875
//#define TARGET_MCU_PIC16F18875
//#define TARGET_MCU_PIC16LF18876
//#define TARGET_MCU_PIC16F18876
//#define TARGET_MCU_PIC16LF18877
//#define TARGET_MCU_PIC16F18877

#endif
